Takazudo/zudo-led-lamp/doc/src/content/docs/architecture/index.mdx

---
title: Architecture
sidebar_position: 1
---

The locked prototype architecture — board split, net tables, final BOM, and the
decisions behind each. This is what the KiCad phase starts from.

<CategoryNav category="architecture" />
