Takazudo/zudo-led-lamp/doc/src/content/docs/power/index.mdx

---
title: Power
sidebar_position: 1
---

Board P — the USB-PD front end that negotiates a 15 V/3 A contract and hands a
switched rail downstream. Audited from the zudo-pd project, with every rating
re-checked against primary datasheets.

<CategoryNav category="power" />
