Takazudo/zudo-led-lamp/doc/src/content/docs/research/index.mdx

---
title: Research
sidebar_position: 1
---

Candidate research feeding the architecture decision — LED and driver options,
thermal budget, interconnect, and the control side (logic rail, MCU, knob,
modulation). Options here are deliberately left open; the picks live in
Architecture.

<CategoryNav category="research" />
