Takazudo/zudo-led-lamp/doc/src/content/docs/components/integration/index.mdx

---
# GENERATED by doc/component-docs — do not edit; run `pnpm generate:components`
title: "Integration"
description: "Cross-component rules — rule-rail-envelope, rule-usb-pd-nvm-load-switch, rule-al8860-led-stage, rule-ap63203-logic-stage, rule-ntc-adc-firmware, rule-evidence-chain, rule-c5446803-power-cut, rule-c470643-brightness-adc — with the records and facts each spans, its conditioned calculations, and what it refuses to conclude."
sidebar_position: 4
---

A component record answers questions about one part. These rules answer the ones that span several — whether a divider built from two resistors keeps a third part inside its own limit, whether a clamp event stays under everything downstream of it. Each rule is projected whole from stored evidence: its conditions, the exact facts it rests on, any conditioned arithmetic, and the exact wording of what it refuses to conclude.

## How to read these rules

- **The refusal is the rule.** — Every rule states, in its own words, what may NOT be concluded from the evidence above it. That sentence is the rule's real output; the verdict is shorthand for it.
- **A verdict belongs to the rule, not to a part.** — A rule's verdict says how far the cross-component question has been settled. It is never a judgement about any of the parts the rule names, and the verdicts are never combined into one.
- **Calculations are conditioned, and the conditions are the point.** — Each calculation publishes its expression, its inputs and the exact results that were recorded, together with the conditions under which the answer means anything. A result read without them is arithmetic mistaken for a measurement.
- **Numbers here were carried, not computed.** — The expressions are published so a reader can redo the arithmetic. This page does not evaluate them — the results shown are the ones the evidence recorded.
- **An evidence chain does not flow downhill.** — A stage being settled says nothing about any stage after it. A document confirming a limit is not a measurement of the assembled board.

## Rules at a glance

<EvidenceAnchor id="integration-index" />

<EvidenceTable label="rules-index">
  | Rule                                                          | Domain                             | Records | Facts | Verdict     |
  | ------------------------------------------------------------- | ---------------------------------- | ------- | ----- | ----------- |
  | [`rule-rail-envelope`](#rule-rail-envelope)                   | rail-envelope                      | 13      | 22    | UNSOURCED   |
  | [`rule-usb-pd-nvm-load-switch`](#rule-usb-pd-nvm-load-switch) | usb-pd-nvm-load-switch             | 9       | 18    | UNSOURCED   |
  | [`rule-al8860-led-stage`](#rule-al8860-led-stage)             | al8860-led-stage                   | 7       | 25    | NEEDS BENCH |
  | [`rule-ap63203-logic-stage`](#rule-ap63203-logic-stage)       | ap63203-logic-stage                | 4       | 16    | UNSOURCED   |
  | [`rule-ntc-adc-firmware`](#rule-ntc-adc-firmware)             | ntc-adc-firmware                   | 3       | 9     | UNSOURCED   |
  | [`rule-evidence-chain`](#rule-evidence-chain)                 | source-to-bench-chain              | 5       | 8     | NEEDS BENCH |
  | [`rule-c5446803-power-cut`](#rule-c5446803-power-cut)         | board-mounted lamp power switching | 4       | 5     | NEEDS BENCH |
  | [`rule-c470643-brightness-adc`](#rule-c470643-brightness-adc) | potentiometer-brightness-adc       | 5       | 12    | NEEDS BENCH |
</EvidenceTable>

## rule-rail-envelope

<EvidenceAnchor id="rule-rail-envelope" />

**What this rule asks:** Whether every part on the input rail stays inside its own recorded limits across a legal power contract, a mis-contract, and a transient clamp event.

**Domain:** rail-envelope

**Verdict:** UNSOURCED

**This rule refuses to conclude:** Do not declare the complete rail safe while STUSB primary trust, project mapping, actual clamp/source-impedance waveform, and harness/as-built evidence remain open.

**Conditions:** Separate legal 5/15 V operation, 20 V mis-contract, and transient clamp behavior; connector-pair current, direct-board mechanics, and upstream source impedance remain independent conditions.

**Records this rule spans:**

- [`rec-type-c-31-m-17`](/docs/components/records/type-c-31-m-17/) — TYPE-C-31-M-17
- [`rec-stusb4500qtr`](/docs/components/records/stusb4500qtr/) — STUSB4500QTR
- [`rec-high-diode-smaj20a`](/docs/components/records/high-diode-smaj20a/) — SMAJ20A
- [`rec-umw-ao3401a`](/docs/components/records/umw-ao3401a/) — AO3401A
- [`rec-bsmd1206-075-30v`](/docs/components/records/bsmd1206-075-30v/) — BSMD1206-075-30V
- [`rec-al8860mp-13`](/docs/components/records/al8860mp-13/) — AL8860MP-13
- [`rec-ap63203wu-7`](/docs/components/records/ap63203wu-7/) — AP63203WU-7
- [`rec-c492405`](/docs/components/records/c492405/) — PZ254V-11-06P
- [`rec-c2832269`](/docs/components/records/c2832269/) — PM254V-11-06-H85
- [`rec-c13585`](/docs/components/records/c13585/) — CL31A106KBHNNNE
- [`rec-c14663`](/docs/components/records/c14663/) — CC0603KRX7R9BB104
- [`rec-c15849`](/docs/components/records/c15849/) — CL10A105KB8NNNC
- [`rec-cl21a226maqnnne`](/docs/components/records/cl21a226maqnnne/) — CL21A226MAQNNNE

**Facts this rule rests on:** each is published in full on the record page that owns it, at the anchor linked here.

- [`fact-type-c-31-m-17-ratings`](/docs/components/records/type-c-31-m-17/#fact-type-c-31-m-17-ratings) on TYPE-C-31-M-17
- [`fact-stusb-supplies`](/docs/components/records/stusb4500qtr/#fact-stusb-supplies) on STUSB4500QTR
- [`fact-stusb-vdd-absolute-max`](/docs/components/records/stusb4500qtr/#fact-stusb-vdd-absolute-max) on STUSB4500QTR
- [`fact-stusb-cc-absolute-max`](/docs/components/records/stusb4500qtr/#fact-stusb-cc-absolute-max) on STUSB4500QTR
- [`fact-stusb-vbus-pin-absolute-max`](/docs/components/records/stusb4500qtr/#fact-stusb-vbus-pin-absolute-max) on STUSB4500QTR
- [`fact-high-diode-smaj20a-clamp`](/docs/components/records/high-diode-smaj20a/#fact-high-diode-smaj20a-clamp) on SMAJ20A
- [`fact-umw-ao3401a-vds`](/docs/components/records/umw-ao3401a/#fact-umw-ao3401a-vds) on AO3401A
- [`fact-umw-ao3401a-vgs`](/docs/components/records/umw-ao3401a/#fact-umw-ao3401a-vgs) on AO3401A
- [`fact-bhfuse-voltage-max`](/docs/components/records/bsmd1206-075-30v/#fact-bhfuse-voltage-max) on BSMD1206-075-30V
- [`fact-al8860-vin-recommended-max`](/docs/components/records/al8860mp-13/#fact-al8860-vin-recommended-max) on AL8860MP-13
- [`fact-al8860-vin-absolute-max`](/docs/components/records/al8860mp-13/#fact-al8860-vin-absolute-max) on AL8860MP-13
- [`fact-ap63203-vin-recommended-max`](/docs/components/records/ap63203wu-7/#fact-ap63203-vin-recommended-max) on AP63203WU-7
- [`fact-ap63203-vin-absolute-dc`](/docs/components/records/ap63203wu-7/#fact-ap63203-vin-absolute-dc) on AP63203WU-7
- [`fact-ap63203-vin-transient`](/docs/components/records/ap63203wu-7/#fact-ap63203-vin-transient) on AP63203WU-7
- [`fact-c492405-current`](/docs/components/records/c492405/#fact-c492405-current) on PZ254V-11-06P
- [`fact-c492405-voltage`](/docs/components/records/c492405/#fact-c492405-voltage) on PZ254V-11-06P
- [`fact-c2832269-current`](/docs/components/records/c2832269/#fact-c2832269-current) on PM254V-11-06-H85
- [`fact-c2832269-voltage`](/docs/components/records/c2832269/#fact-c2832269-voltage) on PM254V-11-06-H85
- [`fact-c13585-voltage`](/docs/components/records/c13585/#fact-c13585-voltage) on CL31A106KBHNNNE
- [`fact-c14663-voltage`](/docs/components/records/c14663/#fact-c14663-voltage) on CC0603KRX7R9BB104
- [`fact-c15849-voltage`](/docs/components/records/c15849/#fact-c15849-voltage) on CL10A105KB8NNNC
- [`fact-cl21-voltage`](/docs/components/records/cl21a226maqnnne/#fact-cl21-voltage) on CL21A226MAQNNNE

### Conditioned calculations

Arithmetic across the facts above. The expression and every input are published so the result can be recomputed rather than trusted, and each carries the conditions under which it means anything at all.

#### calc-stusb-vdd-clamp-overage

<EvidenceAnchor id="calc-stusb-vdd-clamp-overage" />

**Expression:** `fact_high_diode_smaj20a_clamp - fact_stusb_vdd_absolute_max`

**Result:** `overage_v`

**Conditions:** conditioned subtraction of the mirrored 28 V VDD absolute maximum from the High Diode 32.4 V table clamp point; UNSOURCED and not proof of the real VDD transient waveform

**Inputs:**

- [`fact-stusb-vdd-absolute-max`](/docs/components/records/stusb4500qtr/#fact-stusb-vdd-absolute-max) on STUSB4500QTR
- [`fact-high-diode-smaj20a-clamp`](/docs/components/records/high-diode-smaj20a/#fact-high-diode-smaj20a-clamp) on SMAJ20A

| overage\_v |
| ---------- |
| 4.4        |

#### calc-q1-vds-clamp-overage

<EvidenceAnchor id="calc-q1-vds-clamp-overage" />

**Expression:** `fact_high_diode_smaj20a_clamp + fact_umw_ao3401a_vds`

**Result:** `overage_v`

**Conditions:** conditioned magnitude overage above the -30 V Q1 VDS absolute maximum at the 32.4 V clamp table point; actual polarity, waveform, parasitics and as-built state remain open

**Inputs:**

- [`fact-umw-ao3401a-vds`](/docs/components/records/umw-ao3401a/#fact-umw-ao3401a-vds) on AO3401A
- [`fact-high-diode-smaj20a-clamp`](/docs/components/records/high-diode-smaj20a/#fact-high-diode-smaj20a-clamp) on SMAJ20A

| overage\_v |
| ---------- |
| 2.4        |

## rule-usb-pd-nvm-load-switch

<EvidenceAnchor id="rule-usb-pd-nvm-load-switch" />

**What this rule asks:** How the power-delivery controller's stored configuration and its enable output drive the load switch, through every state from detached to fault.

**Domain:** usb-pd-nvm-load-switch

**Verdict:** UNSOURCED

**This rule refuses to conclude:** Do not infer PDOs, VBEN default policy, fitted Rd state, programmed/read-back NVM bytes, or a deterministic 32.4 V VGS violation/safe result without the actual VBEN/gate/source waveform, duration, device/parasitic model, as-built state, and bench evidence.

**Conditions:** Evaluate detached, dead-battery, reset, NVM-loaded, attached, hard-reset, fault, and disconnect states. With VBEN held low and ideal nominal resistors, VGS=-VBUS\*100k/(100k+150k): -6.0 V at 15 V, -8.0 V at 20 V, and -12.96 V at 32.4 V. C35 is gate-to-source, so the nominal small-signal gate time constant is (100k parallel 150k)\*100 nF about 6 ms; device/parasitic behavior and the actual transient waveform remain separate.

**Records this rule spans:**

- [`rec-stusb4500qtr`](/docs/components/records/stusb4500qtr/) — STUSB4500QTR
- [`rec-umw-ao3401a`](/docs/components/records/umw-ao3401a/) — AO3401A
- [`rec-c25803`](/docs/components/records/c25803/) — 0603WAF1003T5E
- [`rec-c22807`](/docs/components/records/c22807/) — 0603WAF1503T5E
- [`rec-c14663`](/docs/components/records/c14663/) — CC0603KRX7R9BB104
- [`rec-c21189`](/docs/components/records/c21189/) — 0603WAF0000T5E
- [`rec-rd-0603waf5101t5e`](/docs/components/records/rd-0603waf5101t5e/) — 0603WAF5101T5E
- [`rec-al8860mp-13`](/docs/components/records/al8860mp-13/) — AL8860MP-13
- [`rec-ap63203wu-7`](/docs/components/records/ap63203wu-7/) — AP63203WU-7

**Facts this rule rests on:** each is published in full on the record page that owns it, at the anchor linked here.

- [`fact-stusb-pin-states`](/docs/components/records/stusb4500qtr/#fact-stusb-pin-states) on STUSB4500QTR
- [`fact-stusb-vben`](/docs/components/records/stusb4500qtr/#fact-stusb-vben) on STUSB4500QTR
- [`fact-stusb-nvm-load`](/docs/components/records/stusb4500qtr/#fact-stusb-nvm-load) on STUSB4500QTR
- [`fact-stusb-volatile-pdo`](/docs/components/records/stusb4500qtr/#fact-stusb-volatile-pdo) on STUSB4500QTR
- [`fact-stusb-artifact`](/docs/components/records/stusb4500qtr/#fact-stusb-artifact) on STUSB4500QTR
- [`fact-umw-ao3401a-vgs`](/docs/components/records/umw-ao3401a/#fact-umw-ao3401a-vgs) on AO3401A
- [`fact-umw-ao3401a-project-nets`](/docs/components/records/umw-ao3401a/#fact-umw-ao3401a-project-nets) on AO3401A
- [`fact-c25803-resistance`](/docs/components/records/c25803/#fact-c25803-resistance) on 0603WAF1003T5E
- [`fact-c22807-resistance`](/docs/components/records/c22807/#fact-c22807-resistance) on 0603WAF1503T5E
- [`fact-c22807-r12-topology`](/docs/components/records/c22807/#fact-c22807-r12-topology) on 0603WAF1503T5E
- [`fact-c14663-capacitance`](/docs/components/records/c14663/#fact-c14663-capacitance) on CC0603KRX7R9BB104
- [`fact-c14663-c35-topology`](/docs/components/records/c14663/#fact-c14663-c35-topology) on CC0603KRX7R9BB104
- [`fact-c21189-ccdb-topology`](/docs/components/records/c21189/#fact-c21189-ccdb-topology) on 0603WAF0000T5E
- [`fact-rd-fit-state`](/docs/components/records/rd-0603waf5101t5e/#fact-rd-fit-state) on 0603WAF5101T5E
- [`fact-al8860-project-nets`](/docs/components/records/al8860mp-13/#fact-al8860-project-nets) on AL8860MP-13
- [`fact-al8860-ctrl`](/docs/components/records/al8860mp-13/#fact-al8860-ctrl) on AL8860MP-13
- [`fact-ap63203-project-nets`](/docs/components/records/ap63203wu-7/#fact-ap63203-project-nets) on AP63203WU-7
- [`fact-ap63203-en-open`](/docs/components/records/ap63203wu-7/#fact-ap63203-en-open) on AP63203WU-7

### Conditioned calculations

Arithmetic across the facts above. The expression and every input are published so the result can be recomputed rather than trusted, and each carries the conditions under which it means anything at all.

#### calc-q1-steady-vgs

<EvidenceAnchor id="calc-q1-steady-vgs" />

**Expression:** `-vbus_v * fact_c25803_resistance / (fact_c25803_resistance + fact_c22807_resistance)`

**Result:** `vgs_v`

**Conditions:** ideal steady VBEN-low divider only; absolute maximum is not an operating target

**Inputs:**

- [`fact-stusb-vben`](/docs/components/records/stusb4500qtr/#fact-stusb-vben) on STUSB4500QTR
- [`fact-c25803-resistance`](/docs/components/records/c25803/#fact-c25803-resistance) on 0603WAF1003T5E
- [`fact-c22807-resistance`](/docs/components/records/c22807/#fact-c22807-resistance) on 0603WAF1503T5E
- [`fact-c22807-r12-topology`](/docs/components/records/c22807/#fact-c22807-r12-topology) on 0603WAF1503T5E

| vbus\_v | vgs\_v |
| --- | --- |
| 15 | -6 |
| 20 | -8 |
| 32.4 | -12.96 |

#### calc-q1-steady-vgs-margin

<EvidenceAnchor id="calc-q1-steady-vgs-margin" />

**Expression:** `fact_umw_ao3401a_vgs - vbus_v * fact_c25803_resistance / (fact_c25803_resistance + fact_c22807_resistance)`

**Result:** `margin_v`

**Conditions:** ideal steady VBEN-low magnitude margin to the 12 V absolute maximum; the negative 32.4 V ideal-steady result is not a deterministic claim about the real transient waveform

**Inputs:**

- [`fact-umw-ao3401a-vgs`](/docs/components/records/umw-ao3401a/#fact-umw-ao3401a-vgs) on AO3401A
- [`fact-c25803-resistance`](/docs/components/records/c25803/#fact-c25803-resistance) on 0603WAF1003T5E
- [`fact-c22807-resistance`](/docs/components/records/c22807/#fact-c22807-resistance) on 0603WAF1503T5E
- [`fact-c22807-r12-topology`](/docs/components/records/c22807/#fact-c22807-r12-topology) on 0603WAF1503T5E

| vbus\_v | margin\_v |
| --- | --- |
| 15 | 6 |
| 20 | 4 |
| 32.4 | -0.96 |

#### calc-q1-gate-tau

<EvidenceAnchor id="calc-q1-gate-tau" />

**Expression:** `(fact_c25803_resistance * fact_c22807_resistance / (fact_c25803_resistance + fact_c22807_resistance)) * fact_c14663_capacitance * 1e-6`

**Result:** `result_s`

**Conditions:** fact-c14663 capacitance is expressed in uF; nominal small-signal RC only; excludes MOSFET capacitance, STUSB output impedance, PCB parasitics and nonlinear switching

**Inputs:**

- [`fact-c25803-resistance`](/docs/components/records/c25803/#fact-c25803-resistance) on 0603WAF1003T5E
- [`fact-c22807-resistance`](/docs/components/records/c22807/#fact-c22807-resistance) on 0603WAF1503T5E
- [`fact-c14663-capacitance`](/docs/components/records/c14663/#fact-c14663-capacitance) on CC0603KRX7R9BB104
- [`fact-c14663-c35-topology`](/docs/components/records/c14663/#fact-c14663-c35-topology) on CC0603KRX7R9BB104

| result\_s |
| --------- |
| 0.006     |

## rule-al8860-led-stage

<EvidenceAnchor id="rule-al8860-led-stage" />

**What this rule asks:** How the LED driver, its sense resistor, inductor, catch diode and per-branch ballast behave together across the LED forward-voltage, tolerance and temperature envelope.

**Domain:** al8860-led-stage

**Verdict:** NEEDS BENCH

**This rule refuses to conclude:** Do not promote mirror-only FXL or R+O SS26 limits, assumed branch sharing, or nominal arithmetic to a guaranteed selected-stage PASS.

**Conditions:** Use the full LED Vf/current/temperature envelope, resistor tolerance/TCR, magnetic current definition, diode polarity/waveform, ballast sharing, CTRL/PWM state, PCB thermal path, and fault behavior.; per-branch sharing is bounded by a locked 0.30 V acceptance limit on the assembled 3-LED string forward-voltage spread

**Records this rule spans:**

- [`rec-al8860mp-13`](/docs/components/records/al8860mp-13/) — AL8860MP-13
- [`rec-rlp25feer200`](/docs/components/records/rlp25feer200/) — RLP25FEER200
- [`rec-fxl0630-330-m`](/docs/components/records/fxl0630-330-m/) — FXL0630-330-M
- [`rec-ro-ss26`](/docs/components/records/ro-ss26/) — SS26
- [`rec-c210315`](/docs/components/records/c210315/) — HL-AM-2835H421W-S1-08-HR3
- [`rec-c2934070`](/docs/components/records/c2934070/) — FRC2512F33R0TS
- [`rec-c4216`](/docs/components/records/c4216/) — 0603WAF3302T5E

**Facts this rule rests on:** each is published in full on the record page that owns it, at the anchor linked here.

- [`fact-al8860-sense-min`](/docs/components/records/al8860mp-13/#fact-al8860-sense-min) on AL8860MP-13
- [`fact-al8860-sense-max`](/docs/components/records/al8860mp-13/#fact-al8860-sense-max) on AL8860MP-13
- [`fact-al8860-current-min`](/docs/components/records/al8860mp-13/#fact-al8860-current-min) on AL8860MP-13
- [`fact-al8860-current-max`](/docs/components/records/al8860mp-13/#fact-al8860-current-max) on AL8860MP-13
- [`fact-al8860-peak-current`](/docs/components/records/al8860mp-13/#fact-al8860-peak-current) on AL8860MP-13
- [`fact-al8860-ctrl`](/docs/components/records/al8860mp-13/#fact-al8860-ctrl) on AL8860MP-13
- [`fact-al8860-faults`](/docs/components/records/al8860mp-13/#fact-al8860-faults) on AL8860MP-13
- [`fact-rlp25-resistance-min`](/docs/components/records/rlp25feer200/#fact-rlp25-resistance-min) on RLP25FEER200
- [`fact-rlp25-resistance-max`](/docs/components/records/rlp25feer200/#fact-rlp25-resistance-max) on RLP25FEER200
- [`fact-rlp25-power-margin`](/docs/components/records/rlp25feer200/#fact-rlp25-power-margin) on RLP25FEER200
- [`fact-fxl-isat-margin`](/docs/components/records/fxl0630-330-m/#fact-fxl-isat-margin) on FXL0630-330-M
- [`fact-ss26-polarity`](/docs/components/records/ro-ss26/#fact-ss26-polarity) on SS26
- [`fact-c210315-vf-min`](/docs/components/records/c210315/#fact-c210315-vf-min) on HL-AM-2835H421W-S1-08-HR3
- [`fact-c210315-vf-max`](/docs/components/records/c210315/#fact-c210315-vf-max) on HL-AM-2835H421W-S1-08-HR3
- [`fact-c210315-forward-current-max`](/docs/components/records/c210315/#fact-c210315-forward-current-max) on HL-AM-2835H421W-S1-08-HR3
- [`fact-c210315-power-max`](/docs/components/records/c210315/#fact-c210315-power-max) on HL-AM-2835H421W-S1-08-HR3
- [`fact-c210315-reverse-voltage-max`](/docs/components/records/c210315/#fact-c210315-reverse-voltage-max) on HL-AM-2835H421W-S1-08-HR3
- [`fact-c210315-junction-temperature-max`](/docs/components/records/c210315/#fact-c210315-junction-temperature-max) on HL-AM-2835H421W-S1-08-HR3
- [`fact-c210315-solder-temperature-max`](/docs/components/records/c210315/#fact-c210315-solder-temperature-max) on HL-AM-2835H421W-S1-08-HR3
- [`fact-c2934070-resistance`](/docs/components/records/c2934070/#fact-c2934070-resistance) on FRC2512F33R0TS
- [`fact-c2934070-power`](/docs/components/records/c2934070/#fact-c2934070-power) on FRC2512F33R0TS
- [`fact-c2934070-rcwv`](/docs/components/records/c2934070/#fact-c2934070-rcwv) on FRC2512F33R0TS
- [`fact-c2934070-topology`](/docs/components/records/c2934070/#fact-c2934070-topology) on FRC2512F33R0TS
- [`fact-c2934070-tolerance`](/docs/components/records/c2934070/#fact-c2934070-tolerance) on FRC2512F33R0TS
- [`fact-c4216-ctrl-topology`](/docs/components/records/c4216/#fact-c4216-ctrl-topology) on 0603WAF3302T5E

### Conditioned calculations

Arithmetic across the facts above. The expression and every input are published so the result can be recomputed rather than trusted, and each carries the conditions under which it means anything at all.

#### calc-led-hot-branch-peak

<EvidenceAnchor id="calc-led-hot-branch-peak" />

**Expression:** `(fact_al8860_peak_current + 7 * spread_v / (fact_c2934070_resistance * (1 + fact_c2934070_tolerance / 100))) / (1 + 7 * (1 - fact_c2934070_tolerance / 100) / (1 + fact_c2934070_tolerance / 100))`

**Result:** `current_a`

**Conditions:** hottest of eight parallel ballast branches at the AL8860 upper peak current, with the hot branch at minimum ballast tolerance and the other seven at maximum; spread\_v is the assembled 3-LED string forward-voltage spread in volts (0 = perfectly matched, 0.3 = the locked acceptance limit, 1.8 = the full retained 2.6-3.2 V window unmitigated); LEDs modelled as fixed forward drops, so this is not proof of the real installed sharing

**Inputs:**

- [`fact-al8860-peak-current`](/docs/components/records/al8860mp-13/#fact-al8860-peak-current) on AL8860MP-13
- [`fact-c2934070-resistance`](/docs/components/records/c2934070/#fact-c2934070-resistance) on FRC2512F33R0TS
- [`fact-c2934070-tolerance`](/docs/components/records/c2934070/#fact-c2934070-tolerance) on FRC2512F33R0TS

| spread\_v | current\_a |
| --- | --- |
| 0 | 0.08017708571864743 |
| 0.3 | 0.08819174108846653 |
| 1.8 | 0.128265017937562 |

#### calc-led-hot-branch-headroom

<EvidenceAnchor id="calc-led-hot-branch-headroom" />

**Expression:** `fact_c210315_forward_current_max - 1000 * (fact_al8860_peak_current + 7 * spread_v / (fact_c2934070_resistance * (1 + fact_c2934070_tolerance / 100))) / (1 + 7 * (1 - fact_c2934070_tolerance / 100) / (1 + fact_c2934070_tolerance / 100))`

**Result:** `headroom_ma`

**Conditions:** milliamp headroom from the hottest branch peak to the 90 mA LED absolute maximum; the spread\_v = 0 result shows the driver's own worst case already consumes 89 percent of the absolute maximum before any Vf mismatch, and spread\_v = 1.8 is negative; absolute maximum is not an operating target and no pulsed-current rating is retained

**Inputs:**

- [`fact-c210315-forward-current-max`](/docs/components/records/c210315/#fact-c210315-forward-current-max) on HL-AM-2835H421W-S1-08-HR3
- [`fact-al8860-peak-current`](/docs/components/records/al8860mp-13/#fact-al8860-peak-current) on AL8860MP-13
- [`fact-c2934070-resistance`](/docs/components/records/c2934070/#fact-c2934070-resistance) on FRC2512F33R0TS
- [`fact-c2934070-tolerance`](/docs/components/records/c2934070/#fact-c2934070-tolerance) on FRC2512F33R0TS

| spread\_v | headroom\_ma |
| --- | --- |
| 0 | 9.822914281352567  |
| 0.3 | 1.8082589115334713 |
| 1.8 | -38.26501793756202 |

## rule-ap63203-logic-stage

<EvidenceAnchor id="rule-ap63203-logic-stage" />

**What this rule asks:** How the logic-rail converter, its inductor and its output capacitor behave together under the real load the microcontroller presents.

**Domain:** ap63203-logic-stage

**Verdict:** UNSOURCED

**This rule refuses to conclude:** Do not infer minimum off-time, MCU load, guaranteed MLCC capacitance, or full-load FNR thermal margin from nominal values.

**Conditions:** Check V15 transients, EN-open startup, switching timing, actual V3P3 load steps, inductor heating/saturation, effective output capacitance, layout, and MCU operating state.

**Records this rule spans:**

- [`rec-ap63203wu-7`](/docs/components/records/ap63203wu-7/) — AP63203WU-7
- [`rec-fnr4030s4r7mt`](/docs/components/records/fnr4030s4r7mt/) — FNR4030S4R7MT
- [`rec-cl21a226maqnnne`](/docs/components/records/cl21a226maqnnne/) — CL21A226MAQNNNE
- [`rec-c529334`](/docs/components/records/c529334/) — STM32G031F8P6

**Facts this rule rests on:** each is published in full on the record page that owns it, at the anchor linked here.

- [`fact-ap63203-vin-recommended-max`](/docs/components/records/ap63203wu-7/#fact-ap63203-vin-recommended-max) on AP63203WU-7
- [`fact-ap63203-vin-absolute-dc`](/docs/components/records/ap63203wu-7/#fact-ap63203-vin-absolute-dc) on AP63203WU-7
- [`fact-ap63203-vin-transient`](/docs/components/records/ap63203wu-7/#fact-ap63203-vin-transient) on AP63203WU-7
- [`fact-ap63203-en-open`](/docs/components/records/ap63203wu-7/#fact-ap63203-en-open) on AP63203WU-7
- [`fact-ap63203-frequency`](/docs/components/records/ap63203wu-7/#fact-ap63203-frequency) on AP63203WU-7
- [`fact-ap63203-min-on-time`](/docs/components/records/ap63203wu-7/#fact-ap63203-min-on-time) on AP63203WU-7
- [`fact-ap63203-min-off-time`](/docs/components/records/ap63203wu-7/#fact-ap63203-min-off-time) on AP63203WU-7
- [`fact-ap63203-required-inductor-current`](/docs/components/records/ap63203wu-7/#fact-ap63203-required-inductor-current) on AP63203WU-7
- [`fact-ap63203-cap-min`](/docs/components/records/ap63203wu-7/#fact-ap63203-cap-min) on AP63203WU-7
- [`fact-ap63203-cap-max`](/docs/components/records/ap63203wu-7/#fact-ap63203-cap-max) on AP63203WU-7
- [`fact-ap63203-thermal`](/docs/components/records/ap63203wu-7/#fact-ap63203-thermal) on AP63203WU-7
- [`fact-fnr-isat-margin`](/docs/components/records/fnr4030s4r7mt/#fact-fnr-isat-margin) on FNR4030S4R7MT
- [`fact-fnr-irated-margin`](/docs/components/records/fnr4030s4r7mt/#fact-fnr-irated-margin) on FNR4030S4R7MT
- [`fact-cl21-dc-bias`](/docs/components/records/cl21a226maqnnne/#fact-cl21-dc-bias) on CL21A226MAQNNNE
- [`fact-cl21-effective-capacitance-status`](/docs/components/records/cl21a226maqnnne/#fact-cl21-effective-capacitance-status) on CL21A226MAQNNNE
- [`fact-c529334-topology`](/docs/components/records/c529334/#fact-c529334-topology) on STM32G031F8P6

**Conditioned calculations:** none are recorded for this rule.

## rule-ntc-adc-firmware

<EvidenceAnchor id="rule-ntc-adc-firmware" />

**What this rule asks:** How the thermistor, its divider, the analog-to-digital input and the firmware that reads them combine into a temperature the design can act on.

**Domain:** ntc-adc-firmware

**Verdict:** UNSOURCED

**This rule refuses to conclude:** Do not invent firmware thresholds or use beta-only conversion as a guaranteed full R-T curve.

**Conditions:** Evaluate NTC tolerance and R-T data, divider loading, ADC sample time/source impedance, calibration, placement/thermal lag, and actual firmware thresholds/hysteresis.; the divider top is 100 kOhm C25803 and the ADC channel requires the 160.5-cycle sample time, with a stated sensing validity floor of -20 C at RT1

**Records this rule spans:**

- [`rec-c13564`](/docs/components/records/c13564/) — NCP18XH103F03RB
- [`rec-c529334`](/docs/components/records/c529334/) — STM32G031F8P6
- [`rec-c25803`](/docs/components/records/c25803/) — 0603WAF1003T5E

**Facts this rule rests on:** each is published in full on the record page that owns it, at the anchor linked here.

- [`fact-c13564-resistance`](/docs/components/records/c13564/#fact-c13564-resistance) on NCP18XH103F03RB
- [`fact-c13564-beta`](/docs/components/records/c13564/#fact-c13564-beta) on NCP18XH103F03RB
- [`fact-c13564-max-current`](/docs/components/records/c13564/#fact-c13564-max-current) on NCP18XH103F03RB
- [`fact-c13564-topology`](/docs/components/records/c13564/#fact-c13564-topology) on NCP18XH103F03RB
- [`fact-c13564-curve-caveat`](/docs/components/records/c13564/#fact-c13564-curve-caveat) on NCP18XH103F03RB
- [`fact-c529334-adc`](/docs/components/records/c529334/#fact-c529334-adc) on STM32G031F8P6
- [`fact-c529334-topology`](/docs/components/records/c529334/#fact-c529334-topology) on STM32G031F8P6
- [`fact-c25803-resistance`](/docs/components/records/c25803/#fact-c25803-resistance) on 0603WAF1003T5E
- [`fact-c25803-tolerance`](/docs/components/records/c25803/#fact-c25803-tolerance) on 0603WAF1003T5E

### Conditioned calculations

Arithmetic across the facts above. The expression and every input are published so the result can be recomputed rather than trusted, and each carries the conditions under which it means anything at all.

#### calc-ntc-divider-current-margin

<EvidenceAnchor id="calc-ntc-divider-current-margin" />

**Expression:** `fact_c13564_max_current - 1000 * rail_v / (fact_c25803_resistance * (1 - fact_c25803_tolerance / 100))`

**Result:** `margin_ma`

**Conditions:** bounding divider current at R26 minimum with the NTC treated as a short, so the result holds at every temperature and under a shorted-thermistor fault; rail\_v 3.33 is fact-ap63203-vout-max and 3.3 is nominal; positive margin\_ma means the installed current stays under Murata's 0.1 mA operating maximum; not a measurement of the real installed current

**Inputs:**

- [`fact-c13564-max-current`](/docs/components/records/c13564/#fact-c13564-max-current) on NCP18XH103F03RB
- [`fact-c25803-resistance`](/docs/components/records/c25803/#fact-c25803-resistance) on 0603WAF1003T5E
- [`fact-c25803-tolerance`](/docs/components/records/c25803/#fact-c25803-tolerance) on 0603WAF1003T5E

| rail\_v | margin\_ma |
| --- | --- |
| 3.33 | 0.06636363636363637 |
| 3.3 | 0.06666666666666668 |

#### calc-ntc-adc-source-impedance

<EvidenceAnchor id="calc-ntc-adc-source-impedance" />

**Expression:** `fact_c25803_resistance * (1 + fact_c25803_tolerance / 100) * r_ntc_ohm / (fact_c25803_resistance * (1 + fact_c25803_tolerance / 100) + r_ntc_ohm)`

**Result:** `r_source_ohm`

**Conditions:** ADC source resistance at R26 maximum; the r\_ntc\_ohm inputs are beta-derived cold-end maxima (-20 C and 25 C) from fact-c13564-resistance and fact-c13564-beta at R25 max and B max, not a guaranteed R-T table per fact-c13564-curve-caveat; compare against the 50 kOhm allowance at 160.5 cycles in fact-c529334-adc

**Inputs:**

- [`fact-c25803-resistance`](/docs/components/records/c25803/#fact-c25803-resistance) on 0603WAF1003T5E
- [`fact-c25803-tolerance`](/docs/components/records/c25803/#fact-c25803-tolerance) on 0603WAF1003T5E

| r\_ntc\_ohm | r\_source\_ohm |
| --- | --- |
| 77314.35 | 43792.0411340983  |
| 10100 | 9181.818181818182 |

## rule-evidence-chain

<EvidenceAnchor id="rule-evidence-chain" />

**What this rule asks:** How far each claim has travelled from a manufacturer document towards a measurement on real hardware, stage by stage.

**Domain:** source-to-bench-chain

**Verdict:** NEEDS BENCH

**This rule refuses to conclude:** A completed upstream stage never implies a later as-built, programmed, or measured stage.

**Conditions:** Trace each claim through official source, conditioned requirement, generated netlist, symbol/footprint pin map, PCB/BOM/CPL identity, as-built inspection, programmed state, and bench evidence.

**Records this rule spans:**

- [`rec-stusb4500qtr`](/docs/components/records/stusb4500qtr/) — STUSB4500QTR
- [`rec-umw-ao3401a`](/docs/components/records/umw-ao3401a/) — AO3401A
- [`rec-al8860mp-13`](/docs/components/records/al8860mp-13/) — AL8860MP-13
- [`rec-ap63203wu-7`](/docs/components/records/ap63203wu-7/) — AP63203WU-7
- [`rec-c529334`](/docs/components/records/c529334/) — STM32G031F8P6

**Facts this rule rests on:** each is published in full on the record page that owns it, at the anchor linked here.

- [`fact-stusb-vben`](/docs/components/records/stusb4500qtr/#fact-stusb-vben) on STUSB4500QTR
- [`fact-stusb-artifact`](/docs/components/records/stusb4500qtr/#fact-stusb-artifact) on STUSB4500QTR
- [`fact-umw-ao3401a-vgs`](/docs/components/records/umw-ao3401a/#fact-umw-ao3401a-vgs) on AO3401A
- [`fact-umw-ao3401a-pinout`](/docs/components/records/umw-ao3401a/#fact-umw-ao3401a-pinout) on AO3401A
- [`fact-umw-ao3401a-project-nets`](/docs/components/records/umw-ao3401a/#fact-umw-ao3401a-project-nets) on AO3401A
- [`fact-al8860-project-nets`](/docs/components/records/al8860mp-13/#fact-al8860-project-nets) on AL8860MP-13
- [`fact-ap63203-project-nets`](/docs/components/records/ap63203wu-7/#fact-ap63203-project-nets) on AP63203WU-7
- [`fact-c529334-topology`](/docs/components/records/c529334/#fact-c529334-topology) on STM32G031F8P6

**Conditioned calculations:** none are recorded for this rule.

### Source-to-bench evidence chain

The stages a claim passes through, in order. A settled stage says nothing about any stage after it: a manufacturer document confirming a limit is not an inspection of the assembled board, and neither is a measurement. A stage with no facts against it is not one nobody got round to filling in: nothing has been established there yet, so the rule's conditions and its refusal above are the whole of what is known about it.

<EvidenceTable label="evidence-chain">
  | Stage                   | Status | Facts at this stage                                                                                                                                                                                                                                                                                                                           |
  | ----------------------- | ------ | --------------------------------------------------------------------------------------------------------------------------------------------------------------------------------------------------------------------------------------------------------------------------------------------------------------------------------------------- |
  | official-source         | MIXED  | [`fact-stusb-vben`](/docs/components/records/stusb4500qtr/#fact-stusb-vben) on STUSB4500QTR, [`fact-umw-ao3401a-vgs`](/docs/components/records/umw-ao3401a/#fact-umw-ao3401a-vgs) on AO3401A                                                                                                                                                  |
  | conditioned-requirement | MIXED  | [`fact-stusb-artifact`](/docs/components/records/stusb4500qtr/#fact-stusb-artifact) on STUSB4500QTR, [`fact-umw-ao3401a-vgs`](/docs/components/records/umw-ao3401a/#fact-umw-ao3401a-vgs) on AO3401A                                                                                                                                          |
  | generated-netlist       | MIXED  | [`fact-umw-ao3401a-project-nets`](/docs/components/records/umw-ao3401a/#fact-umw-ao3401a-project-nets) on AO3401A, [`fact-al8860-project-nets`](/docs/components/records/al8860mp-13/#fact-al8860-project-nets) on AL8860MP-13, [`fact-ap63203-project-nets`](/docs/components/records/ap63203wu-7/#fact-ap63203-project-nets) on AP63203WU-7 |
  | symbol-footprint        | MIXED  | [`fact-umw-ao3401a-pinout`](/docs/components/records/umw-ao3401a/#fact-umw-ao3401a-pinout) on AO3401A, [`fact-c529334-topology`](/docs/components/records/c529334/#fact-c529334-topology) on STM32G031F8P6                                                                                                                                    |
  | pcb-orientation         | OPEN   | no fact is recorded at this stage                                                                                                                                                                                                                                                                                                             |
  | bom-cpl                 | OPEN   | no fact is recorded at this stage                                                                                                                                                                                                                                                                                                             |
  | as-built                | OPEN   | no fact is recorded at this stage                                                                                                                                                                                                                                                                                                             |
  | programmed              | OPEN   | no fact is recorded at this stage                                                                                                                                                                                                                                                                                                             |
  | bench                   | OPEN   | no fact is recorded at this stage                                                                                                                                                                                                                                                                                                             |
</EvidenceTable>

## rule-c5446803-power-cut

<EvidenceAnchor id="rule-c5446803-power-cut" />

**Domain:** board-mounted lamp power switching

**Verdict:** NEEDS BENCH

**This rule refuses to conclude:** Do not certify physical OFF isolation, installed height, switch endurance or rail safety from a mirrored current rating and generated design alone.

**Conditions:** SW2 center common 2 receives V15\_FUSED and joins outer pin 1 to switched V15 in ON. In OFF it joins isolated outer pin 3, which has no PCB net but is fused-feed live. Both converters lose normal supply in OFF while Board P remains powered. G020 has a 2 mm actuator and 5.5 mm body-plus-actuator dimension; the corrected model retains shoulder stand-off for approximately 6 mm PCB reach, requiring physical confirmation. Verify inrush, bounce, restart, contact life, rail decay and service-interface back-power. Exact switch drawing remains manufacturer-mirror evidence.

**Records this rule spans:**

- [`rec-c5446803`](/docs/components/records/c5446803/) — SS-12D01-G020
- [`rec-bsmd1206-075-30v`](/docs/components/records/bsmd1206-075-30v/) — BSMD1206-075-30V
- [`rec-al8860mp-13`](/docs/components/records/al8860mp-13/) — AL8860MP-13
- [`rec-ap63203wu-7`](/docs/components/records/ap63203wu-7/) — AP63203WU-7

**Facts this rule rests on:** each is published in full on the record page that owns it, at the anchor linked here.

- [`fact-c5446803-rating`](/docs/components/records/c5446803/#fact-c5446803-rating) on SS-12D01-G020
- [`fact-c5446803-terminals`](/docs/components/records/c5446803/#fact-c5446803-terminals) on SS-12D01-G020
- [`fact-c5446803-project-nets`](/docs/components/records/c5446803/#fact-c5446803-project-nets) on SS-12D01-G020
- [`fact-bhfuse-project-nets`](/docs/components/records/bsmd1206-075-30v/#fact-bhfuse-project-nets) on BSMD1206-075-30V
- [`fact-ap63203-en-open`](/docs/components/records/ap63203wu-7/#fact-ap63203-en-open) on AP63203WU-7

**Conditioned calculations:** none are recorded for this rule.

## rule-c470643-brightness-adc

<EvidenceAnchor id="rule-c470643-brightness-adc" />

**Domain:** potentiometer-brightness-adc

**Verdict:** NEEDS BENCH

**This rule refuses to conclude:** Do not claim calibrated absolute brightness, safe startup, open-wiper fault detection or installed mechanical fit from schematic calculations and unflashed firmware examples.

**Conditions:** RV1 RK10J11E0034 is the single-unit 10 kOhm +/-30% stopped potentiometer: end 1=GND, end 3=V3P3, wiper 2 through R27 100 Ohm to U3.7 PA0 BRIGHT\_ADC; all four mechanical pads and U3.8 are no-connects. R22 100 kOhm and C22 100 nF connect BRIGHT\_ADC to GND. Worst divider source resistance is 3.25 kOhm plus 100 Ohm before bias loading; open-wiper nominal RC decay is 10 ms, not a certified fault detector. Use the documented 160.5-cycle ADC target, reference/errata review, endpoint and inversion calibration, averaging and startup ramp with thermal/PD gates. The 270-degree physical stops replace quadrature behavior. The catalog lists Insertion (t: 2 mm); this is not treated as a mandatory PCB thickness. Seating and contact life on the actual 1.6 mm PCB need prototype proof, and firmware is not flashed.

**Records this rule spans:**

- [`rec-c470643`](/docs/components/records/c470643/) — RK10J11E0034
- [`rec-c529334`](/docs/components/records/c529334/) — STM32G031F8P6
- [`rec-c22775`](/docs/components/records/c22775/) — 0603WAF1000T5E
- [`rec-c25803`](/docs/components/records/c25803/) — 0603WAF1003T5E
- [`rec-c14663`](/docs/components/records/c14663/) — CC0603KRX7R9BB104

**Facts this rule rests on:** each is published in full on the record page that owns it, at the anchor linked here.

- [`fact-c470643-resistance`](/docs/components/records/c470643/#fact-c470643-resistance) on RK10J11E0034
- [`fact-c470643-tolerance`](/docs/components/records/c470643/#fact-c470643-tolerance) on RK10J11E0034
- [`fact-c470643-terminals`](/docs/components/records/c470643/#fact-c470643-terminals) on RK10J11E0034
- [`fact-c470643-stops`](/docs/components/records/c470643/#fact-c470643-stops) on RK10J11E0034
- [`fact-c470643-project-nets`](/docs/components/records/c470643/#fact-c470643-project-nets) on RK10J11E0034
- [`fact-c470643-adc-design`](/docs/components/records/c470643/#fact-c470643-adc-design) on RK10J11E0034
- [`fact-c470643-firmware-target`](/docs/components/records/c470643/#fact-c470643-firmware-target) on RK10J11E0034
- [`fact-c529334-adc`](/docs/components/records/c529334/#fact-c529334-adc) on STM32G031F8P6
- [`fact-c529334-topology`](/docs/components/records/c529334/#fact-c529334-topology) on STM32G031F8P6
- [`fact-c22775-brightness-topology`](/docs/components/records/c22775/#fact-c22775-brightness-topology) on 0603WAF1000T5E
- [`fact-c25803-resistance`](/docs/components/records/c25803/#fact-c25803-resistance) on 0603WAF1003T5E
- [`fact-c14663-capacitance`](/docs/components/records/c14663/#fact-c14663-capacitance) on CC0603KRX7R9BB104

**Conditioned calculations:** none are recorded for this rule.

## Legend

What the recorded terms on this page mean, in ordinary words. The exact terms above are the ones that count; these descriptions explain them and never replace them.

### Rule verdict

| Recorded term | What it means |
| --- | --- |
| NEEDS BENCH | Cannot be settled from documents. It needs measurement on real hardware before it can be relied on. |
| UNSOURCED | No accepted source backs this value yet. Treat it as a claim, not a fact. |

### Domain

| Recorded term | What it means |
| --- | --- |
| al8860-led-stage | How the LED driver, its sense resistor, inductor, catch diode and per-branch ballast behave together across the LED forward-voltage, tolerance and temperature envelope. |
| ap63203-logic-stage | How the logic-rail converter, its inductor and its output capacitor behave together under the real load the microcontroller presents. |
| board-mounted lamp power switching | No plain-language description is recorded for this term yet. |
| ntc-adc-firmware | How the thermistor, its divider, the analog-to-digital input and the firmware that reads them combine into a temperature the design can act on. |
| potentiometer-brightness-adc | No plain-language description is recorded for this term yet. |
| rail-envelope | Whether every part on the input rail stays inside its own recorded limits across a legal power contract, a mis-contract, and a transient clamp event. |
| source-to-bench-chain | How far each claim has travelled from a manufacturer document towards a measurement on real hardware, stage by stage. |
| usb-pd-nvm-load-switch | How the power-delivery controller's stored configuration and its enable output drive the load switch, through every state from detached to fault. |

### Evidence stage

| Recorded term | What it means |
| --- | --- |
| as-built | The assembled board has been inspected and matches what was specified. |
| bench | The behaviour has been measured on powered hardware. |
| bom-cpl | The exact orderable part and its placement are confirmed in the assembly files.  |
| conditioned-requirement | The claim has been restated as a requirement with the conditions it holds under. |
| generated-netlist | The requirement is reflected in the netlist the project generates. |
| official-source | The claim appears in a document the manufacturer published. |
| pcb-orientation | The part's orientation and pad mapping are confirmed on the board layout. |
| programmed | The device's stored configuration has been written and read back. |
| symbol-footprint | The schematic symbol's pins are mapped onto the footprint's pads. |

### Evidence stage status

| Recorded term | What it means |
| --- | --- |
| MIXED | Some claims at this stage are settled and others are not. It is not a completed stage, and the facts listed against it are the ones that carry it. |
| OPEN | Nothing at this stage has been established yet. A completed earlier stage does not imply it. |

## Raw agent resource

These rules are generated from a stored evidence bundle and do not restate it. The bundle is the source of truth: where the two ever disagree, the bundle is right and this page is stale.

- [Open the owning bundle](/docs/claude-skills/circuit-spec-integration/) `circuit-spec-integration`
