Takazudo/zudo-led-lamp/doc/src/content/docs/claude-skills/component-gswitch-ss-12d01-g020/index.mdx

---
title: component-gswitch-ss-12d01-g020
description: Use to audit exact SS-12D01-G020 C5446803 low-profile maintained power slider, manufacturer evidence, JLCPCB sourcing, PCB pin mapping and prototype requirements.
sidebar_label: component-gswitch-ss-12d01-g020
generated: true
---

# SS-12D01-G020 low-profile maintained power slider

Run component-spec-audit first and read every JSON file in this owner. Use circuit-spec-integration for cross-component behavior. The exact part is fitted on Board L and sourced through JLCPCB; supplier stock is a dated observation, not a reservation or assembled-board proof.

SW2 is non-shorting SPDT. The reviewed project pin convention uses center 2 for fused input, outer 1 for V15, and outer 3 without a PCB net; terminal 3 is internally live in OFF. The manufacturer drawing is unnumbered and distributor-mirrored. G020 means 2 mm actuator projection above the 3.5 mm body; a generic 8 mm model is not the exact variant. Retain mirror-trust, inrush/contact-life and physical OFF/back-power gates.

## Human component reference

Generated [C5446803 record](/docs/components/records/c5446803/), [catalog](/docs/components/catalog/) and [integration](/docs/components/integration/). JSON evidence remains authoritative.
