Takazudo/zudo-led-lamp/doc/src/content/docs/claude-skills/component-type-c-31-m-17/index.mdx

---
title: component-type-c-31-m-17
description: Audit the exact HRO TYPE-C-31-M-17 C283540 USB-C receptacle. Use for Board P J1 contacts, shell, duplicate pads, orientation, footprint, ratings, bring-up, or substitution.
sidebar_label: component-type-c-31-m-17
generated: true
---

# TYPE-C-31-M-17

Run the central validator and read every local artifact. The official HRO page and Rev A drawing confirm the exact MPN, current/voltage, dielectric, insulation, contact-resistance, durability, temperature, and mechanical facts; the stable distributor mirror binds C283540. Reject Korean Hroparts Elec and other vendor substitutions. Do not promote the older mirror's superseded 3,000-cycle value or the conflicting +85 °C locale claim.

The primary contact sketch does not by itself prove the project's numeric symbol-to-pad mapping. Before assembly, mechanically compare the incoming part against pad centers, shell tabs, board edge, mating face, and orientation. Before PD, continuity-map both VBUS contacts, both grounds, CC1, CC2, and shell with no cable and both plug orientations.

## Human component reference

Human projection of this bundle: [rec-type-c-31-m-17](/docs/components/records/type-c-31-m-17/). Those pages are generated from the JSON files here and add nothing to them — where the two disagree, this bundle is correct. See also the [component catalog](/docs/components/catalog/) and the [cross-component rules](/docs/components/integration/).
