Takazudo/zudo-led-lamp/doc/src/content/docs/claude-skills/component-xfcn-board-headers/index.mdx

---
title: component-xfcn-board-headers
description: Audit the exact XFCN PZ254V-11-06P C492405 male and PM254V-11-06-H85 C2832269 female six-position 2.54 mm board-to-board headers. Use for Boards P/L pin order, orientation, footprint, ratings, mating,...
sidebar_label: component-xfcn-board-headers
generated: true
---

# XFCN 2.54 mm board-to-board headers

Run the central validator and read every local artifact. Board P JOUT1 is the male PZ254V-11-06P; Board L J2 is the female PM254V-11-06-H85. The manufacturer drawings explicitly specify the reciprocal PZ254/PM254 single-row series as mates.

The parts are unkeyed. Before powering mated boards, verify both PCB pin-1 marks, the physical board-to-board orientation, the six-net end-to-end map, standoff/alignment, full seating, and mechanical retention. The catalog mating statement does not prove the current PCB placements or enclosure mechanics.

## Human component reference

Human projections of this bundle: [PZ254V-11-06P](/docs/components/records/c492405/) and [PM254V-11-06-H85](/docs/components/records/c2832269/). Those pages are generated from the JSON files here and add nothing to them — where the two disagree, this bundle is correct. See also the [component catalog](/docs/components/catalog/) and the [cross-component rules](/docs/components/integration/).
