Takazudo/zudo-led-lamp/doc/src/content/docs/components/records/index.mdx

---
# GENERATED by doc/component-docs — do not edit; run `pnpm generate:components`
title: "Records"
description: "Per-record evidence pages: facts, sources, coverage domains, pin maps and interactions."
sidebar_position: 3
---

One page per published component record, each carrying that record's facts, sources, coverage domains, pin maps and interactions. They are ordered as the bill of materials orders them, with each subordinate record directly after the part it belongs to.

To compare records against each other, start from the [catalog](/docs/components/catalog/).

## Records

- [TYPE-C-31-M-17](/docs/components/records/type-c-31-m-17/) — `rec-type-c-31-m-17` USB-C receptacle
- [STUSB4500QTR](/docs/components/records/stusb4500qtr/) — `rec-stusb4500qtr` USB-PD sink controller
- [PESD24VS1UB,115](/docs/components/records/pesd24vs1ub/) — `rec-pesd24vs1ub` CC-line ESD protection
- [0603WAF5101T5E](/docs/components/records/rd-0603waf5101t5e/) — `rec-rd-0603waf5101t5e` external USB-C Rd resistor
- [AO3401A](/docs/components/records/umw-ao3401a/) — `rec-umw-ao3401a` P-channel load-switch MOSFET
- [SMAJ20A](/docs/components/records/high-diode-smaj20a/) — `rec-high-diode-smaj20a` 20 V TVS diode
- [CL31A106KBHNNNE](/docs/components/records/c13585/) — `rec-c13585` 10 uF 50 V MLCC
- [CC0603KRX7R9BB104](/docs/components/records/c14663/) — `rec-c14663` 100 nF 50 V MLCC
- [CL10A105KB8NNNC](/docs/components/records/c15849/) — `rec-c15849` 1 uF 50 V MLCC
- [0603WAF1003T5E](/docs/components/records/c25803/) — `rec-c25803` 100 kOhm resistor
- [0603WAF1503T5E](/docs/components/records/c22807/) — `rec-c22807` 150 kOhm resistor
- [0603WAF4700T5E](/docs/components/records/c23179/) — `rec-c23179` 470 Ohm resistor
- [0603WAF4701T5E](/docs/components/records/c23162/) — `rec-c23162` 4.7 kOhm resistor
- [0603WAF0000T5E](/docs/components/records/c21189/) — `rec-c21189` zero-Ohm CCDB bridge
- [0805W8F1002T5E](/docs/components/records/c17414/) — `rec-c17414` 10 kOhm resistor
- [PZ254V-11-06P](/docs/components/records/c492405/) — `rec-c492405` male board-to-board header
- [PM254V-11-06-H85](/docs/components/records/c2832269/) — `rec-c2832269` female board-to-board header
- [BSMD1206-075-30V](/docs/components/records/bsmd1206-075-30v/) — `rec-bsmd1206-075-30v` 750 mA PPTC fuse
- [AL8860MP-13](/docs/components/records/al8860mp-13/) — `rec-al8860mp-13` buck LED driver
- [RLP25FEER200](/docs/components/records/rlp25feer200/) — `rec-rlp25feer200` 200 mOhm current-sense resistor
- [FXL0630-330-M](/docs/components/records/fxl0630-330-m/) — `rec-fxl0630-330-m` 33 uH LED buck inductor
- [SS26](/docs/components/records/ro-ss26/) — `rec-ro-ss26` 60 V Schottky catch diode
- [AP63203WU-7](/docs/components/records/ap63203wu-7/) — `rec-ap63203wu-7` 3.3 V synchronous buck converter
- [FNR4030S4R7MT](/docs/components/records/fnr4030s4r7mt/) — `rec-fnr4030s4r7mt` 4.7 uH logic buck inductor
- [CL21A226MAQNNNE](/docs/components/records/cl21a226maqnnne/) — `rec-cl21a226maqnnne` 22 uF 25 V buck output MLCC
- [STM32G031F8P6](/docs/components/records/c529334/) — `rec-c529334` control MCU
- [PZ254V-11-05P](/docs/components/records/c492404/) — `rec-c492404` hand-fit SWD header
- [DS254P-2X10-L0](/docs/components/records/c4749199/) — `rec-c4749199` ST-LINK/V2 20-pin adapter header
- [RK10J11E0034](/docs/components/records/c470643/) — `rec-c470643` stopped brightness potentiometer
- [NCP18XH103F03RB](/docs/components/records/c13564/) — `rec-c13564` 10 kOhm NTC thermistor
- [0603WAF3302T5E](/docs/components/records/c4216/) — `rec-c4216` 33 kOhm resistor
- [0603WAF1000T5E](/docs/components/records/c22775/) — `rec-c22775` 100 Ohm brightness ADC series resistor
- [HL-AM-2835H421W-S1-08-HR3](/docs/components/records/c210315/) — `rec-c210315` 3000 K 2835 LED
- [FRC2512F33R0TS](/docs/components/records/c2934070/) — `rec-c2934070` 33 Ohm LED ballast resistor
- [SS-12D01-G020](/docs/components/records/c5446803/) — `rec-c5446803` maintained lamp power slider
