Takazudo/zudo-led-lamp/doc/src/content/docs/components/records/al8860mp-13/index.mdx

---
# GENERATED by doc/component-docs — do not edit; run `pnpm generate:components`
title: "AL8860MP-13"
description: "buck LED driver — Diodes Incorporated — C500782 — board-l U2 — rec-al8860mp-13"
sidebar_position: 20
---

<EvidenceAnchor id="rec-al8860mp-13" />

Everything below is projected from this project's stored component evidence. Values keep the exact wording, conditions, units and verdicts they were recorded with — nothing here is re-typed, corrected, or combined into an overall judgement about the part.

This record in the catalog: [AL8860MP-13](/docs/components/catalog/#rec-al8860mp-13)

## Identity

| Field | Recorded value |
| --- | --- |
| Record ID | `rec-al8860mp-13` |
| Record kind | standalone |
| Manufacturer part number | `AL8860MP-13` |
| Manufacturer | Diodes Incorporated |
| Function | buck LED driver |
| LCSC ID | `C500782` |
| Package | `MSOP-8_L3.0-W3.0-P0.65-LS4.9-BL-EP1.8` |
| Inventory line | `line-c500782` |
| Also known as | `hysteretic LED driver` |
| Owner skill | `component-al8860mp-13` |

**Fit:** Fitted

**Identity state:** UNRESOLVED

**Source state:** SOURCE UNAVAILABLE

**Coverage:** 1 open of 4 published

## Documents and package

<EvidenceAnchor id="component-references-heading" />

<ComponentReferences descriptor="7b2276657273696f6e223a312c22646f63756d656e74223a7b226c6162656c223a2244617461736865657420504446222c227469746c65223a22414c383836302034305620312e3541204275636b204c454420447269766572222c22617574686f72697479223a224d414e5546414354555245525f5052494d415259222c22617661696c6162696c697479223a22415641494c41424c45222c2275726c223a2268747470733a2f2f7777772e64696f6465732e636f6d2f6461746173686565742f646f776e6c6f61642f414c383836302e706466227d2c22666f6f747072696e74223a7b226e616d65223a224d534f502d385f4c332e302d57332e302d50302e36352d4c53342e392d424c2d4550312e38222c22617373657455726c223a222f6173736574732f636f6d706f6e656e742d70726576696577732f666f6f747072696e74732f4d534f502d385f4c332e302d57332e302d50302e36352d4c53342e392d424c2d4550312e382e737667227d2c226d6f64656c44657363726970746f72223a22376232323736363537323733363936663665323233613331326332323730363136333662363136373635343936343232336132323464353334663530326433383566346333333265333032643537333332653330326435303330326533363335326434633533333432653339326434323463326434353530333132653338323232633232373036313633366236313637363534633631363236353663323233613232346435333466353032643338356634633333326533303264353733333265333032643530333032653336333532643463353333343265333932643432346332643435353033313265333832323263323236643666363436353663353537323663323233613232326636313733373336353734373332663633366636643730366636653635366537343264373037323635373636393635373737333266366436663634363536633733326634643533346635303264333835663463333332653330326435373333326533303264353033303265333633353264346335333334326533393264343234633264343535303331326533383265373737323663323232633232366636363636373336353734323233613762323237383232336133303263323237393232336133303263323237613232336133303764326332323732366637343631373436393666366532323361376232323738323233613330326332323739323233613330326332323761323233613330376432633232373336333631366336353232336137623232373832323361333132633232373932323361333132633232376132323361333137643764227d" />

**Selected document:** [Datasheet PDF](https://www.diodes.com/datasheet/download/AL8860.pdf) — AL8860 40V 1.5A Buck LED Driver

**Selected source ID:** `src-al8860-ds39014`

**Authority:** MANUFACTURER\_PRIMARY

**Availability:** AVAILABLE

**Package footprint:** `MSOP-8_L3.0-W3.0-P0.65-LS4.9-BL-EP1.8`

This geometry represents a shared footprint package and may not exactly match the manufacturer part.

## Placements

Every position this exact line occupies in the as-built design. One line may be placed many times and across more than one board.

| Board | Reference designator |
| --- | --- |
| board-l | `U2` |

## Coverage

Coverage is stated one domain at a time and is never rolled up. A domain marked open is a question that has not been answered; it is not a finding that the part is unsuitable. A record with no open domains has not thereby been declared safe.

### pin-topology-and-ep

<EvidenceAnchor id="cov-al8860-pin-topology" />

**Coverage ID:** `cov-al8860-pin-topology` · **Status:** COVERED

**Reason:** fact-al8860-topology, fact-al8860-pin-ep, fact-al8860-project-nets

**Facts in this domain:**

- [`fact-al8860-topology`](#fact-al8860-topology)
- [`fact-al8860-pin-ep`](#fact-al8860-pin-ep)
- [`fact-al8860-project-nets`](#fact-al8860-project-nets)

### limits-control-timing-faults

<EvidenceAnchor id="cov-al8860-limits-control" />

**Coverage ID:** `cov-al8860-limits-control` · **Status:** COVERED

**Reason:** fact-al8860-vin-recommended-max through fact-al8860-faults, plus fact-al8860-duty-band (DS39014 Rev 8-2, Electrical Characteristics table row DSW Recommended Duty Cycle Range, re-verified 2026-08-02 against the currently live diodes.com PDF, hash-matched to the retained mirror)

**Facts in this domain:**

- [`fact-al8860-vin-recommended-max`](#fact-al8860-vin-recommended-max)
- [`fact-al8860-vin-absolute-max`](#fact-al8860-vin-absolute-max)
- [`fact-al8860-sense-min`](#fact-al8860-sense-min)
- [`fact-al8860-sense-max`](#fact-al8860-sense-max)
- [`fact-al8860-current-min`](#fact-al8860-current-min)
- [`fact-al8860-current-max`](#fact-al8860-current-max)
- [`fact-al8860-ripple-fraction`](#fact-al8860-ripple-fraction)
- [`fact-al8860-peak-current`](#fact-al8860-peak-current)
- [`fact-al8860-ctrl`](#fact-al8860-ctrl)
- [`fact-al8860-min-on-time`](#fact-al8860-min-on-time)
- [`fact-al8860-max-frequency`](#fact-al8860-max-frequency)
- [`fact-al8860-inductance-min`](#fact-al8860-inductance-min)
- [`fact-al8860-inductance-max`](#fact-al8860-inductance-max)
- [`fact-al8860-faults`](#fact-al8860-faults)
- [`fact-al8860-duty-band`](#fact-al8860-duty-band)

### layout-and-thermal

<EvidenceAnchor id="cov-al8860-layout" />

**Coverage ID:** `cov-al8860-layout` · **Status:** COVERED

**Reason:** fact-al8860-layout

**Facts in this domain:**

- [`fact-al8860-layout`](#fact-al8860-layout)

### led-string-voltage-temperature

<EvidenceAnchor id="cov-al8860-led-domain" />

**Coverage ID:** `cov-al8860-led-domain` · **Status:** OPEN

**Reason:** Exact LED VF versus current/temperature and switching-node overshoot require the LED/integration records and bench waveform.

**Facts in this domain:** none are recorded against it.

**Blocked by:** no blocking fact is recorded. What is missing has not been reduced to a specific recorded fact, so the reason above is the whole of what is known.

## Facts

Each fact keeps its value, its unit, the conditions it holds under, where it came from and how far it has been confirmed as separate fields, because they are separate claims. A value without its conditions is not the same fact, and a verdict is about the evidence for the value, not about the part.

### ABSOLUTE\_MAXIMUM

A never-exceed limit. Reaching it may damage the part; it is not an operating target and there is no margin implied by it.

<EvidenceFact>
  <EvidenceAnchor id="fact-al8860-vin-absolute-max" />

  **Fact:** `fact-al8860-vin-absolute-max`

  **Value:** 42 · **Unit:** `V`

  **Conditions:** stress rating only, TA=25 C

  **Verdict:** PASS - primary-source confirmed · **Provenance:** PRIMARY-SPEC

  **Evidence:** [src-al8860-ds39014: Absolute Maximum Ratings table row VIN](#src-al8860-ds39014)
</EvidenceFact>

### RECOMMENDED\_OPERATION

The range the manufacturer intends the part to be used in. Always narrower than the absolute maximum.

<EvidenceFact>
  <EvidenceAnchor id="fact-al8860-topology" />

  **Fact:** `fact-al8860-topology`

  **Value:** hysteretic buck LED driver with integrated NDMOS and high-side current sense · **Unit:** `NONE`

  **Conditions:** normal buck operation

  **Verdict:** PASS - primary-source confirmed · **Provenance:** PRIMARY-SPEC

  **Evidence:** [src-al8860-ds39014: Section Application Information and Figure Typical Application Circuit](#src-al8860-ds39014)
</EvidenceFact>

<EvidenceFact>
  <EvidenceAnchor id="fact-al8860-pin-ep" />

  **Fact:** `fact-al8860-pin-ep`

  **Value:** EP connects to GND thermal mass but is not an electrical ground conduction path · **Unit:** `NONE`

  **Conditions:** MSOP-8EP package

  **Verdict:** PASS - primary-source confirmed · **Provenance:** PRIMARY-SPEC

  **Evidence:** [src-al8860-ds39014: Pin Descriptions table row EP](#src-al8860-ds39014)
</EvidenceFact>

<EvidenceFact>
  <EvidenceAnchor id="fact-al8860-vin-recommended-max" />

  **Fact:** `fact-al8860-vin-recommended-max`

  **Value:** 40 · **Unit:** `V`

  **Conditions:** functional input range, TA=25 C unless specified

  **Verdict:** PASS - primary-source confirmed · **Provenance:** PRIMARY-SPEC

  **Evidence:** [src-al8860-ds39014: Recommended Operating Conditions table row VIN](#src-al8860-ds39014)
</EvidenceFact>

<EvidenceFact>
  <EvidenceAnchor id="fact-al8860-ctrl" />

  **Fact:** `fact-al8860-ctrl`

  **Value:** floating gives normal operation; below 0.2 V disables; 0.3-2.5 V analog dims; PWM below 500 Hz preserves best range · **Unit:** `NONE`

  **Conditions:** CTRL pin operation

  **Verdict:** PASS - primary-source confirmed · **Provenance:** PRIMARY-SPEC

  **Evidence:** [src-al8860-ds39014: Pin Descriptions table row CTRL and Application Information section PWM Dimming](#src-al8860-ds39014)
</EvidenceFact>

<EvidenceFact>
  <EvidenceAnchor id="fact-al8860-min-on-time" />

  **Fact:** `fact-al8860-min-on-time`

  **Value:** 500 · **Unit:** `ns`

  **Conditions:** recommended minimum switch on-time for 4% accuracy

  **Verdict:** PASS - primary-source confirmed · **Provenance:** PRIMARY-SPEC

  **Evidence:** [src-al8860-ds39014: Electrical Characteristics table row tON\_REC](#src-al8860-ds39014)
</EvidenceFact>

<EvidenceFact>
  <EvidenceAnchor id="fact-al8860-max-frequency" />

  **Fact:** `fact-al8860-max-frequency`

  **Value:** 1 · **Unit:** `MHz`

  **Conditions:** recommended maximum switch frequency

  **Verdict:** PASS - primary-source confirmed · **Provenance:** PRIMARY-SPEC

  **Evidence:** [src-al8860-ds39014: Electrical Characteristics table row fSW(MAX)](#src-al8860-ds39014)
</EvidenceFact>

<EvidenceFact>
  <EvidenceAnchor id="fact-al8860-inductance-min" />

  **Fact:** `fact-al8860-inductance-min`

  **Value:** 33 · **Unit:** `uH`

  **Conditions:** recommended AL8860 inductor range

  **Verdict:** PASS - primary-source confirmed · **Provenance:** PRIMARY-SPEC

  **Evidence:** [src-al8860-ds39014: Section Inductor Selection row recommended range](#src-al8860-ds39014)
</EvidenceFact>

<EvidenceFact>
  <EvidenceAnchor id="fact-al8860-inductance-max" />

  **Fact:** `fact-al8860-inductance-max`

  **Value:** 100 · **Unit:** `uH`

  **Conditions:** recommended AL8860 inductor range

  **Verdict:** PASS - primary-source confirmed · **Provenance:** PRIMARY-SPEC

  **Evidence:** [src-al8860-ds39014: Section Inductor Selection row recommended range](#src-al8860-ds39014)
</EvidenceFact>

<EvidenceFact>
  <EvidenceAnchor id="fact-al8860-faults" />

  **Fact:** `fact-al8860-faults`

  **Value:** open LED stops oscillation; shorted LED chain remains regulated but changes duty and frequency; OTP restarts after hysteresis · **Unit:** `NONE`

  **Conditions:** documented open, short, and overtemperature states

  **Verdict:** PASS - primary-source confirmed · **Provenance:** PRIMARY-SPEC

  **Evidence:** [src-al8860-ds39014: Sections Thermal Protection, Open Circuit LEDs, and LED Chain Shorted Together](#src-al8860-ds39014)
</EvidenceFact>

<EvidenceFact>
  <EvidenceAnchor id="fact-al8860-duty-band" />

  **Fact:** `fact-al8860-duty-band`

  **Value:** 25 to 75 · **Unit:** `%`

  **Conditions:** DSW parameter, internal buck-switch operating duty-cycle recommended range, guaranteed by design; distinct from the 98% DSW(MAX) absolute maximum duty cycle and from the 5-100% CTRL-pin analog-dimming range

  **Verdict:** PASS - primary-source confirmed · **Provenance:** PRIMARY-SPEC

  **Evidence:** [src-al8860-ds39014: Electrical Characteristics table row DSW Recommended Duty Cycle Range](#src-al8860-ds39014)
</EvidenceFact>

### GUARANTEED\_ELECTRICAL

A parameter the manufacturer guarantees over the stated conditions, usually with minimum, typical and maximum values.

<EvidenceFact>
  <EvidenceAnchor id="fact-al8860-sense-min" />

  **Fact:** `fact-al8860-sense-min`

  **Value:** 0.096 · **Unit:** `V`

  **Conditions:** SET relative to VIN, TA=25 C unless specified

  **Verdict:** PASS - primary-source confirmed · **Provenance:** PRIMARY-SPEC

  **Evidence:** [src-al8860-ds39014: Electrical Characteristics table row VSENSE minimum](#src-al8860-ds39014)
</EvidenceFact>

<EvidenceFact>
  <EvidenceAnchor id="fact-al8860-sense-max" />

  **Fact:** `fact-al8860-sense-max`

  **Value:** 0.104 · **Unit:** `V`

  **Conditions:** SET relative to VIN, TA=25 C unless specified

  **Verdict:** PASS - primary-source confirmed · **Provenance:** PRIMARY-SPEC

  **Evidence:** [src-al8860-ds39014: Electrical Characteristics table row VSENSE maximum](#src-al8860-ds39014)
</EvidenceFact>

<EvidenceFact>
  <EvidenceAnchor id="fact-al8860-ripple-fraction" />

  **Fact:** `fact-al8860-ripple-fraction`

  **Value:** 0.4 · **Unit:** `ratio`

  **Conditions:** internally set coil peak-to-peak ripple relative to ILED

  **Verdict:** PASS - primary-source confirmed · **Provenance:** PRIMARY-SPEC

  **Evidence:** [src-al8860-ds39014: Section Inductor Selection equation definitions row delta-I](#src-al8860-ds39014)
</EvidenceFact>

### THERMAL\_SOA

Thermal and safe-operating-area behaviour: how much the part may dissipate, and under what mounting and ambient conditions.

<EvidenceFact>
  <EvidenceAnchor id="fact-al8860-layout" />

  **Fact:** `fact-al8860-layout`

  **Value:** place input capacitor and inductor close; use low-resistance SW path; connect EP to thermal mass · **Unit:** `NONE`

  **Conditions:** MSOP-8EP implementation

  **Verdict:** PASS - primary-source confirmed · **Provenance:** PRIMARY-SPEC

  **Evidence:** [src-al8860-ds39014: Pin Descriptions table row EP and Sections Capacitor Selection and Inductor Selection](#src-al8860-ds39014)
</EvidenceFact>

### PROJECT\_STATE

A value this project recorded about how the part is used here — a chosen operating point, a net assignment, or a derived figure. Not a manufacturer specification.

<EvidenceFact>
  <EvidenceAnchor id="fact-al8860-manufacturer" />

  **Fact:** `fact-al8860-manufacturer`

  **Value:** Diodes Incorporated · **Unit:** `NONE`

  **Conditions:** exact AL8860MP-13 orderable identity

  **Verdict:** PASS - primary-source confirmed · **Provenance:** PRIMARY-SPEC

  **Evidence:** [src-al8860-ds39014: title block and ordering table row AL8860MP-13](#src-al8860-ds39014)
</EvidenceFact>

<EvidenceFact>
  <EvidenceAnchor id="fact-al8860-current-min" />

  **Fact:** `fact-al8860-current-min`

  **Value:** 0.4752475247524752 · **Unit:** `A`

  **Conditions:** CTRL floating, minimum sense threshold and maximum initial sense resistance at 25 C; TCR and self-heating unresolved

  **Verdict:** NEEDS BENCH · **Provenance:** CALCULATED

  **Evidence:** [`src-al8860-ds39014`](#src-al8860-ds39014) — CALCULATED: fact-al8860-sense-min divided by fact-rlp25-resistance-max
</EvidenceFact>

<EvidenceFact>
  <EvidenceAnchor id="fact-al8860-current-max" />

  **Fact:** `fact-al8860-current-max`

  **Value:** 0.5252525252525252 · **Unit:** `A`

  **Conditions:** CTRL floating, maximum sense threshold and minimum initial sense resistance at 25 C; TCR and self-heating unresolved

  **Verdict:** NEEDS BENCH · **Provenance:** CALCULATED

  **Evidence:** [`src-al8860-ds39014`](#src-al8860-ds39014) — CALCULATED: fact-al8860-sense-max divided by fact-rlp25-resistance-min
</EvidenceFact>

<EvidenceFact>
  <EvidenceAnchor id="fact-al8860-peak-current" />

  **Fact:** `fact-al8860-peak-current`

  **Value:** 0.6303030303030303 · **Unit:** `A`

  **Conditions:** upper sense threshold, minimum initial 1% sense resistance, half of 40% peak-to-peak ripple above mean; TCR and self-heating unresolved

  **Verdict:** NEEDS BENCH · **Provenance:** CALCULATED

  **Evidence:** [`src-al8860-ds39014`](#src-al8860-ds39014) — CALCULATED: fact-al8860-current-max times one plus fact-al8860-ripple-fraction divided by two
</EvidenceFact>

<EvidenceFact>
  <EvidenceAnchor id="fact-al8860-project-nets" />

  **Fact:** `fact-al8860-project-nets`

  **Value:** U2.8=V15; U2.1=SET; U2.4=CTRL; U2.5/6=LED\_N; U2.2/3/9=GND; U2.7=NC · **Unit:** `NONE`

  **Conditions:** current generated Board L source

  **Verdict:** NOT APPLICABLE · **Provenance:** PROJECT-CHOICE

  **Evidence:** [src-al8860-generator: COMPONENTS table row U2, NETS rows, and NO\_CONNECT row U2.7](#src-al8860-generator)
</EvidenceFact>

## Calculation dependencies

These values were derived from other recorded facts rather than read from a document. The expression and every input are published so the number can be recomputed instead of trusted. A derived value is never stronger than the weakest fact it depends on.

**Fact:** [`fact-al8860-current-min`](#fact-al8860-current-min)

**Expression:** `fact_al8860_sense_min / fact_rlp25_resistance_max`

**Depends on:**

- [`fact-al8860-sense-min`](#fact-al8860-sense-min)
- [`fact-rlp25-resistance-max`](/docs/components/records/rlp25feer200/#fact-rlp25-resistance-max) on RLP25FEER200

**Fact:** [`fact-al8860-current-max`](#fact-al8860-current-max)

**Expression:** `fact_al8860_sense_max / fact_rlp25_resistance_min`

**Depends on:**

- [`fact-al8860-sense-max`](#fact-al8860-sense-max)
- [`fact-rlp25-resistance-min`](/docs/components/records/rlp25feer200/#fact-rlp25-resistance-min) on RLP25FEER200

**Fact:** [`fact-al8860-peak-current`](#fact-al8860-peak-current)

**Expression:** `fact_al8860_current_max * (1 + fact_al8860_ripple_fraction / 2)`

**Depends on:**

- [`fact-al8860-current-max`](#fact-al8860-current-max)
- [`fact-al8860-ripple-fraction`](#fact-al8860-ripple-fraction)

## Pin maps

The mapping between schematic pins and PCB pads, or physical terminals for an external part, as recorded. A record may carry more than one map when the same part is documented in more than one context.

### pinmap-al8860

<EvidenceAnchor id="pinmap-al8860" />

- **Symbol:** `AL8860MP-13`
- **Footprint:** `MSOP-8_L3.0-W3.0-P0.65-LS4.9-BL-EP1.8`
- **Pins:** 9

<EvidenceDetails label="pin-assignments">
  <EvidenceTable label="pin-assignments">
    | Symbol pin | Name   | Footprint pad | Function                                       |
    | ---------- | ------ | ------------- | ---------------------------------------------- |
    | `1`        | `SET`  | `1`           | sense input; Board L SET                       |
    | `2`        | `GND`  | `2`           | ground                                         |
    | `3`        | `GND`  | `3`           | ground                                         |
    | `4`        | `CTRL` | `4`           | PWM/analog control                             |
    | `5`        | `SW`   | `5`           | switch drain; LED\_N                           |
    | `6`        | `SW`   | `6`           | switch drain; LED\_N                           |
    | `7`        | `NC`   | `7`           | no connection                                  |
    | `8`        | `VIN`  | `8`           | V15 input                                      |
    | `9`        | `EP`   | `9`           | GND thermal pad, not current-return substitute |
  </EvidenceTable>
</EvidenceDetails>

## Interactions

Behaviour that is not a property of this part alone. Each interaction names the records it spans, the conditions it holds under, and how far it has been confirmed. An interaction that spans several parts appears on every one of their pages, under the same identifier, because it is equally a fact about each.

### int-al8860-control

<EvidenceAnchor id="int-al8860-control" />

- **Records involved:** `rec-al8860mp-13` (this record)
- **Conditions:** CTRL driven by Board L PWM\_DIM with analog/PWM state and frequency verified
- **Verdict:** NEEDS BENCH

**Facts this rests on:**

- [`fact-al8860-ctrl`](#fact-al8860-ctrl)
- [`fact-al8860-min-on-time`](#fact-al8860-min-on-time)
- [`fact-al8860-max-frequency`](#fact-al8860-max-frequency)
- [`fact-al8860-project-nets`](#fact-al8860-project-nets)

### int-al8860-power-stage

<EvidenceAnchor id="int-al8860-power-stage" />

- **Records involved:** `rec-al8860mp-13` (this record), [`rec-rlp25feer200`](/docs/components/records/rlp25feer200/), [`rec-fxl0630-330-m`](/docs/components/records/fxl0630-330-m/), [`rec-ro-ss26`](/docs/components/records/ro-ss26/)
- **Conditions:** full LED-string VF/temperature, V15 transient, layout parasitics, and PWM operating envelope
- **Verdict:** NEEDS BENCH

**Facts this rests on:**

- [`fact-al8860-peak-current`](#fact-al8860-peak-current)
- [`fact-rlp25-power-margin`](/docs/components/records/rlp25feer200/#fact-rlp25-power-margin) on RLP25FEER200
- [`fact-fxl-isat-margin`](/docs/components/records/fxl0630-330-m/#fact-fxl-isat-margin) on FXL0630-330-M
- [`fact-ss26-voltage-margin`](/docs/components/records/ro-ss26/#fact-ss26-voltage-margin) on SS26
- [`fact-ss26-current-margin`](/docs/components/records/ro-ss26/#fact-ss26-current-margin) on SS26

## Cross-component rules

Rules that span several parts at once and are published in full on the integration page. Each rule's verdict below is that rule's own — it is a statement about the cross-component question, not about this part — and the exact wording of what the rule refuses to conclude is published with the rule itself.

- [`rule-rail-envelope`](/docs/components/integration/#rule-rail-envelope) — rail-envelope — **rule verdict:** UNSOURCED — Whether every part on the input rail stays inside its own recorded limits across a legal power contract, a mis-contract, and a transient clamp event.
- [`rule-usb-pd-nvm-load-switch`](/docs/components/integration/#rule-usb-pd-nvm-load-switch) — usb-pd-nvm-load-switch — **rule verdict:** UNSOURCED — How the power-delivery controller's stored configuration and its enable output drive the load switch, through every state from detached to fault.
- [`rule-al8860-led-stage`](/docs/components/integration/#rule-al8860-led-stage) — al8860-led-stage — **rule verdict:** NEEDS BENCH — How the LED driver, its sense resistor, inductor, catch diode and per-branch ballast behave together across the LED forward-voltage, tolerance and temperature envelope.
- [`rule-evidence-chain`](/docs/components/integration/#rule-evidence-chain) — source-to-bench-chain — **rule verdict:** NEEDS BENCH — How far each claim has travelled from a manufacturer document towards a measurement on real hardware, stage by stage.
- [`rule-c5446803-power-cut`](/docs/components/integration/#rule-c5446803-power-cut) — board-mounted lamp power switching — **rule verdict:** NEEDS BENCH

[All cross-component rules](/docs/components/integration/)

## Sources

Every document cited above, with its identification, when it was retrieved, and what kind of authority it carries. Sources that could not be retrieved are listed too, with their unavailability stated, so a gap in the evidence is visible rather than absent.

### AL8860 40V 1.5A Buck LED Driver

<EvidenceAnchor id="src-al8860-ds39014" />

**Source ID:** `src-al8860-ds39014` · **Authority:** MANUFACTURER\_PRIMARY

| Field | Recorded value |
| --- | --- |
| Document number | DS39014 |
| Revision | Rev. 8-2 |
| Document date | 2026-04 |
| Retrieved | 2026-08-02 |
| Printed page | 2 of 18 |

**Locator:** Pin Descriptions table; Absolute Maximum and Recommended Operating Conditions tables; Electrical Characteristics table; Application Information sections

**Availability:** AVAILABLE

**Document URL:** [https://www.diodes.com/datasheet/download/AL8860.pdf](https://www.diodes.com/datasheet/download/AL8860.pdf)

### Board L generated schematic specification

<EvidenceAnchor id="src-al8860-generator" />

**Source ID:** `src-al8860-generator` · **Authority:** PROJECT\_GENERATOR

| Field | Recorded value |
| --- | --- |
| Document number | scripts/schgen/board\_l\_spec.py |
| Revision | 410bc1a342286dd6c205d6dcec0f248b8a963987 |
| Document date | 2026-08-02 |
| Retrieved | 2026-08-02 |
| Printed page | source file |

**Locator:** COMPONENTS table row U2 and NETS rows V15, SET, LED\_N, CTRL, PWM\_DIM, and GND

**Availability:** AVAILABLE

**Document URL:** [https://raw.githubusercontent.com/Takazudo/zudo-led-lamp/410bc1a342286dd6c205d6dcec0f248b8a963987/scripts/schgen/board\_l\_spec.py](https://raw.githubusercontent.com/Takazudo/zudo-led-lamp/410bc1a342286dd6c205d6dcec0f248b8a963987/scripts/schgen/board_l_spec.py)

## Legend

What the recorded terms on this page mean, in ordinary words. The exact terms above are the ones that count; these descriptions explain them and never replace them.

### Verdict

| Recorded term | What it means |
| --- | --- |
| `NEEDS BENCH` | Cannot be settled from documents. It needs measurement on real hardware before it can be relied on. |
| `NOT APPLICABLE` | The parameter does not apply to this part as it is used here. |
| `PASS - primary-source confirmed` | Confirmed against the manufacturer's own document for this exact part. |

### Provenance

| Recorded term | What it means |
| --- | --- |
| `CALCULATED` | Derived arithmetically from other facts listed here. The expression and every input are shown, so the number can be recomputed rather than trusted. |
| `PRIMARY-SPEC` | Taken from the manufacturer's own specification document. |
| `PROJECT-CHOICE` | A decision made by this project. No vendor asserts it. |

### Fact class

| Recorded term | What it means |
| --- | --- |
| `ABSOLUTE_MAXIMUM` | A never-exceed limit. Reaching it may damage the part; it is not an operating target and there is no margin implied by it. |
| `GUARANTEED_ELECTRICAL` | A parameter the manufacturer guarantees over the stated conditions, usually with minimum, typical and maximum values. |
| `PROJECT_STATE` | A value this project recorded about how the part is used here — a chosen operating point, a net assignment, or a derived figure. Not a manufacturer specification. |
| `RECOMMENDED_OPERATION` | The range the manufacturer intends the part to be used in. Always narrower than the absolute maximum. |
| `THERMAL_SOA` | Thermal and safe-operating-area behaviour: how much the part may dissipate, and under what mounting and ambient conditions. |

### Coverage status

| Recorded term | What it means |
| --- | --- |
| `COVERED` | Every question this domain asks is answered by the facts listed against it. |
| `OPEN` | Unresolved. Open means the question has not been answered, not that the part is unsafe — the reason states what is missing. |

### Source availability

| Recorded term | What it means |
| --- | --- |
| `AVAILABLE` | The document was retrieved and is on record. |

### Source authority

| Recorded term | What it means |
| --- | --- |
| `MANUFACTURER_PRIMARY` | The manufacturer's own document for this exact part. |
| `PROJECT_GENERATOR` | A document this project generated, such as a schematic or netlist export. |

### Identity state

| Recorded term | What it means |
| --- | --- |
| `UNRESOLVED`  | The exact orderable part is not yet confirmed. Substituting a same-name part from another vendor is not permitted on that basis. |

### Source state

| Recorded term | What it means |
| --- | --- |
| `SOURCE UNAVAILABLE` | No document backing this line could be retrieved. |

### Unit

| Recorded term | What it means |
| --- | --- |
| `NONE` | The value is not a physical quantity, so it carries no unit. Recorded as \`NONE\`. |

## Raw agent resource

This page is generated from a stored evidence bundle and does not restate it. The bundle is the source of truth: where the two ever disagree, the bundle is right and this page is stale.

[Open the owning bundle](/docs/claude-skills/component-al8860mp-13/) `component-al8860mp-13`
