Takazudo/zudo-led-lamp/doc/src/content/docs/components/records/ap63203wu-7/index.mdx

---
# GENERATED by doc/component-docs — do not edit; run `pnpm generate:components`
title: "AP63203WU-7"
description: "3.3 V synchronous buck converter — Diodes Incorporated — C780769 — board-l U4 — rec-ap63203wu-7"
sidebar_position: 24
---

<EvidenceAnchor id="rec-ap63203wu-7" />

Everything below is projected from this project's stored component evidence. Values keep the exact wording, conditions, units and verdicts they were recorded with — nothing here is re-typed, corrected, or combined into an overall judgement about the part.

This record in the catalog: [AP63203WU-7](/docs/components/catalog/#rec-ap63203wu-7)

## Identity

| Field | Recorded value |
| --- | --- |
| Record ID | `rec-ap63203wu-7` |
| Record kind | standalone |
| Manufacturer part number | `AP63203WU-7` |
| Manufacturer | Diodes Incorporated |
| Function | 3.3 V synchronous buck converter |
| LCSC ID | `C780769` |
| Package | `TSOT-26_L2.9-W1.6-P0.95-LS2.8-BL` |
| Inventory line | `line-c780769` |
| Also known as | `logic buck` |
| Owner skill | `component-ap63203wu-7` |

**Fit:** Fitted

**Identity state:** UNRESOLVED

**Source state:** SOURCE UNAVAILABLE

**Coverage:** 2 open of 4 published

## Documents and package

<EvidenceAnchor id="component-references-heading" />

<ComponentReferences descriptor="7b2276657273696f6e223a312c22646f63756d656e74223a7b226c6162656c223a2244617461736865657420504446222c227469746c65223a22415036333230302f415036333230312f415036333230332f4150363332303520332e385620746f2033325620496e7075742032412053796e6368726f6e6f7573204275636b222c22617574686f72697479223a224d414e5546414354555245525f5052494d415259222c22617661696c6162696c697479223a22415641494c41424c45222c2275726c223a2268747470733a2f2f7777772e64696f6465732e636f6d2f6461746173686565742f646f776e6c6f61642f415036333230302d415036333230312d415036333230332d415036333230352e706466227d2c22666f6f747072696e74223a7b226e616d65223a2254534f542d32365f4c322e392d57312e362d50302e39352d4c53322e382d424c222c22617373657455726c223a222f6173736574732f636f6d706f6e656e742d70726576696577732f666f6f747072696e74732f54534f542d32365f4c322e392d57312e362d50302e39352d4c53322e382d424c2e737667227d2c226d6f64656c44657363726970746f72223a22376232323736363537323733363936663665323233613331326332323730363136333662363136373635343936343232336132323534353334663534326433323336356634633332326533393264353733313265333632643530333032653339333532643463353333323265333832643432346332323263323237303631363336623631363736353463363136323635366332323361323235343533346635343264333233363566346333323265333932643537333132653336326435303330326533393335326434633533333232653338326434323463323232633232366436663634363536633535373236633232336132323266363137333733363537343733326636333666366437303666366536353665373432643730373236353736363936353737373332663664366636343635366337333266353435333466353432643332333635663463333232653339326435373331326533363264353033303265333933353264346335333332326533383264343234633265373737323663323232633232366636363636373336353734323233613762323237383232336133303263323237393232336133303263323237613232336133303764326332323732366637343631373436393666366532323361376232323738323233613330326332323739323233613330326332323761323233613330376432633232373336333631366336353232336137623232373832323361333132633232373932323361333132633232376132323361333137643764227d" />

**Selected document:** [Datasheet PDF](https://www.diodes.com/datasheet/download/AP63200-AP63201-AP63203-AP63205.pdf) — AP63200/AP63201/AP63203/AP63205 3.8V to 32V Input 2A Synchronous Buck

**Selected source ID:** `src-ap6320x-ds41326`

**Authority:** MANUFACTURER\_PRIMARY

**Availability:** AVAILABLE

**Package footprint:** `TSOT-26_L2.9-W1.6-P0.95-LS2.8-BL`

This geometry represents a shared footprint package and may not exactly match the manufacturer part.

## Placements

Every position this exact line occupies in the as-built design. One line may be placed many times and across more than one board.

| Board | Reference designator |
| --- | --- |
| board-l | `U4` |

## Coverage

Coverage is stated one domain at a time and is never rolled up. A domain marked open is a question that has not been answered; it is not a finding that the part is unsuitable. A record with no open domains has not thereby been declared safe.

### topology-pins-limits-startup-faults

<EvidenceAnchor id="cov-ap63203-core" />

**Coverage ID:** `cov-ap63203-core` · **Status:** COVERED

**Reason:** fact-ap63203-topology through fact-ap63203-hiccup and fact-ap63203-project-nets

**Facts in this domain:**

- [`fact-ap63203-topology`](#fact-ap63203-topology)
- [`fact-ap63203-en-open`](#fact-ap63203-en-open)
- [`fact-ap63203-vin-recommended-max`](#fact-ap63203-vin-recommended-max)
- [`fact-ap63203-vin-absolute-dc`](#fact-ap63203-vin-absolute-dc)
- [`fact-ap63203-vin-transient`](#fact-ap63203-vin-transient)
- [`fact-ap63203-vout-min`](#fact-ap63203-vout-min)
- [`fact-ap63203-vout-max`](#fact-ap63203-vout-max)
- [`fact-ap63203-frequency`](#fact-ap63203-frequency)
- [`fact-ap63203-min-on-time`](#fact-ap63203-min-on-time)
- [`fact-ap63203-soft-start`](#fact-ap63203-soft-start)
- [`fact-ap63203-peak-limit-min`](#fact-ap63203-peak-limit-min)
- [`fact-ap63203-hiccup`](#fact-ap63203-hiccup)

### lc-envelope-compensation-and-layout

<EvidenceAnchor id="cov-ap63203-lc" />

**Coverage ID:** `cov-ap63203-lc` · **Status:** COVERED

**Reason:** fact-ap63203-inductor-min through fact-ap63203-layout

**Facts in this domain:**

- [`fact-ap63203-inductor-min`](#fact-ap63203-inductor-min)
- [`fact-ap63203-inductor-max`](#fact-ap63203-inductor-max)
- [`fact-ap63203-load-max`](#fact-ap63203-load-max)
- [`fact-ap63203-current-headroom`](#fact-ap63203-current-headroom)
- [`fact-ap63203-required-inductor-current`](#fact-ap63203-required-inductor-current)
- [`fact-ap63203-dcr-max`](#fact-ap63203-dcr-max)
- [`fact-ap63203-cap-min`](#fact-ap63203-cap-min)
- [`fact-ap63203-cap-max`](#fact-ap63203-cap-max)
- [`fact-ap63203-reference-l`](#fact-ap63203-reference-l)
- [`fact-ap63203-reference-cap`](#fact-ap63203-reference-cap)
- [`fact-ap63203-thermal`](#fact-ap63203-thermal)
- [`fact-ap63203-layout`](#fact-ap63203-layout)

### minimum-off-time

<EvidenceAnchor id="cov-ap63203-off" />

**Coverage ID:** `cov-ap63203-off` · **Status:** OPEN

**Reason:** DS41326 gives 80 ns minimum on-time but no minimum off-time; the 220 ns bootstrap refresh interval is a different behavior.

**Facts in this domain:** none are recorded against it.

**Blocked by:** no blocking fact is recorded. What is missing has not been reduced to a specific recorded fact, so the reason above is the whole of what is known.

### project-load-transients-and-thermal

<EvidenceAnchor id="cov-ap63203-load" />

**Coverage ID:** `cov-ap63203-load` · **Status:** OPEN

**Reason:** The generated source does not bound V3P3 load steps, sustained load, copper thermal impedance, or V15 transients.

**Facts in this domain:** none are recorded against it.

**Blocked by:** no blocking fact is recorded. What is missing has not been reduced to a specific recorded fact, so the reason above is the whole of what is known.

## Facts

Each fact keeps its value, its unit, the conditions it holds under, where it came from and how far it has been confirmed as separate fields, because they are separate claims. A value without its conditions is not the same fact, and a verdict is about the evidence for the value, not about the part.

### ABSOLUTE\_MAXIMUM

A never-exceed limit. Reaching it may damage the part; it is not an operating target and there is no margin implied by it.

<EvidenceFact>
  <EvidenceAnchor id="fact-ap63203-vin-absolute-dc" />

  **Fact:** `fact-ap63203-vin-absolute-dc`

  **Value:** 35 · **Unit:** `V`

  **Conditions:** DC stress rating only

  **Verdict:** PASS - primary-source confirmed · **Provenance:** PRIMARY-SPEC

  **Evidence:** [src-ap6320x-ds41326: Absolute Maximum Ratings table row VIN DC](#src-ap6320x-ds41326)
</EvidenceFact>

### RECOMMENDED\_OPERATION

The range the manufacturer intends the part to be used in. Always narrower than the absolute maximum.

<EvidenceFact>
  <EvidenceAnchor id="fact-ap63203-topology" />

  **Fact:** `fact-ap63203-topology`

  **Value:** fixed 3.3 V synchronous peak-current-mode buck with integrated compensation and PFM at light load · **Unit:** `NONE`

  **Conditions:** AP63203 variant

  **Verdict:** PASS - primary-source confirmed · **Provenance:** PRIMARY-SPEC

  **Evidence:** [src-ap6320x-ds41326: Features table rows AP63203 and Section PWM/PFM Operation](#src-ap6320x-ds41326)
</EvidenceFact>

<EvidenceFact>
  <EvidenceAnchor id="fact-ap63203-vin-recommended-max" />

  **Fact:** `fact-ap63203-vin-recommended-max`

  **Value:** 32 · **Unit:** `V`

  **Conditions:** functional input range

  **Verdict:** PASS - primary-source confirmed · **Provenance:** PRIMARY-SPEC

  **Evidence:** [src-ap6320x-ds41326: Recommended Operating Conditions table row VIN](#src-ap6320x-ds41326)
</EvidenceFact>

<EvidenceFact>
  <EvidenceAnchor id="fact-ap63203-inductor-min" />

  **Fact:** `fact-ap63203-inductor-min`

  **Value:** 2.2 · **Unit:** `uH`

  **Conditions:** general recommended inductor envelope

  **Verdict:** PASS - primary-source confirmed · **Provenance:** PRIMARY-SPEC

  **Evidence:** [src-ap6320x-ds41326: Section Inductor row recommended range](#src-ap6320x-ds41326)
</EvidenceFact>

<EvidenceFact>
  <EvidenceAnchor id="fact-ap63203-inductor-max" />

  **Fact:** `fact-ap63203-inductor-max`

  **Value:** 10 · **Unit:** `uH`

  **Conditions:** general recommended inductor envelope

  **Verdict:** PASS - primary-source confirmed · **Provenance:** PRIMARY-SPEC

  **Evidence:** [src-ap6320x-ds41326: Section Inductor row recommended range](#src-ap6320x-ds41326)
</EvidenceFact>

<EvidenceFact>
  <EvidenceAnchor id="fact-ap63203-load-max" />

  **Fact:** `fact-ap63203-load-max`

  **Value:** 2 · **Unit:** `A`

  **Conditions:** maximum continuous output design point

  **Verdict:** PASS - primary-source confirmed · **Provenance:** PRIMARY-SPEC

  **Evidence:** [src-ap6320x-ds41326: Features table row continuous output current](#src-ap6320x-ds41326)
</EvidenceFact>

<EvidenceFact>
  <EvidenceAnchor id="fact-ap63203-current-headroom" />

  **Fact:** `fact-ap63203-current-headroom`

  **Value:** 0.35 · **Unit:** `ratio`

  **Conditions:** recommended inductor DC current rating headroom over maximum load

  **Verdict:** PASS - primary-source confirmed · **Provenance:** PRIMARY-SPEC

  **Evidence:** [src-ap6320x-ds41326: Section Inductor row DC current rating at least 35% higher](#src-ap6320x-ds41326)
</EvidenceFact>

<EvidenceFact>
  <EvidenceAnchor id="fact-ap63203-dcr-max" />

  **Fact:** `fact-ap63203-dcr-max`

  **Value:** 0.1 · **Unit:** `ohm`

  **Conditions:** inductor DCR for highest efficiency

  **Verdict:** PASS - primary-source confirmed · **Provenance:** PRIMARY-SPEC

  **Evidence:** [src-ap6320x-ds41326: Section Inductor row DCR less than 100mOhm](#src-ap6320x-ds41326)
</EvidenceFact>

<EvidenceFact>
  <EvidenceAnchor id="fact-ap63203-cap-min" />

  **Fact:** `fact-ap63203-cap-min`

  **Value:** 22 · **Unit:** `uF`

  **Conditions:** general low-ESR ceramic output capacitance envelope

  **Verdict:** PASS - primary-source confirmed · **Provenance:** PRIMARY-SPEC

  **Evidence:** [src-ap6320x-ds41326: Section Output Capacitor row 22uF to 68uF](#src-ap6320x-ds41326)
</EvidenceFact>

<EvidenceFact>
  <EvidenceAnchor id="fact-ap63203-cap-max" />

  **Fact:** `fact-ap63203-cap-max`

  **Value:** 68 · **Unit:** `uF`

  **Conditions:** general low-ESR ceramic output capacitance envelope

  **Verdict:** PASS - primary-source confirmed · **Provenance:** PRIMARY-SPEC

  **Evidence:** [src-ap6320x-ds41326: Section Output Capacitor row 22uF to 68uF](#src-ap6320x-ds41326)
</EvidenceFact>

### GUARANTEED\_ELECTRICAL

A parameter the manufacturer guarantees over the stated conditions, usually with minimum, typical and maximum values.

<EvidenceFact>
  <EvidenceAnchor id="fact-ap63203-vout-min" />

  **Fact:** `fact-ap63203-vout-min`

  **Value:** 3.27 · **Unit:** `V`

  **Conditions:** CCM, recommended ambient/input range

  **Verdict:** PASS - primary-source confirmed · **Provenance:** PRIMARY-SPEC

  **Evidence:** [src-ap6320x-ds41326: Electrical Characteristics table row AP63203 VFB minimum](#src-ap6320x-ds41326)
</EvidenceFact>

<EvidenceFact>
  <EvidenceAnchor id="fact-ap63203-vout-max" />

  **Fact:** `fact-ap63203-vout-max`

  **Value:** 3.33 · **Unit:** `V`

  **Conditions:** CCM, recommended ambient/input range

  **Verdict:** PASS - primary-source confirmed · **Provenance:** PRIMARY-SPEC

  **Evidence:** [src-ap6320x-ds41326: Electrical Characteristics table row AP63203 VFB maximum](#src-ap6320x-ds41326)
</EvidenceFact>

<EvidenceFact>
  <EvidenceAnchor id="fact-ap63203-frequency" />

  **Fact:** `fact-ap63203-frequency`

  **Value:** 1.1 · **Unit:** `MHz`

  **Conditions:** AP63203 oscillator typical with +/-6% frequency spread spectrum

  **Verdict:** NEEDS BENCH · **Provenance:** PRIMARY-SPEC

  **Evidence:** [src-ap6320x-ds41326: Electrical Characteristics table rows fSW and FSS](#src-ap6320x-ds41326)
</EvidenceFact>

<EvidenceFact>
  <EvidenceAnchor id="fact-ap63203-min-on-time" />

  **Fact:** `fact-ap63203-min-on-time`

  **Value:** 80 · **Unit:** `ns`

  **Conditions:** minimum on-time typical table value

  **Verdict:** NEEDS BENCH · **Provenance:** PRIMARY-SPEC

  **Evidence:** [src-ap6320x-ds41326: Electrical Characteristics table row tON](#src-ap6320x-ds41326)
</EvidenceFact>

<EvidenceFact>
  <EvidenceAnchor id="fact-ap63203-soft-start" />

  **Fact:** `fact-ap63203-soft-start`

  **Value:** 4 · **Unit:** `ms`

  **Conditions:** built-in soft-start typical

  **Verdict:** NEEDS BENCH · **Provenance:** PRIMARY-SPEC

  **Evidence:** [src-ap6320x-ds41326: Electrical Characteristics table row tSS and Section Enable](#src-ap6320x-ds41326)
</EvidenceFact>

<EvidenceFact>
  <EvidenceAnchor id="fact-ap63203-peak-limit-min" />

  **Fact:** `fact-ap63203-peak-limit-min`

  **Value:** 2.5 · **Unit:** `A`

  **Conditions:** high-side cycle-by-cycle peak current limit minimum

  **Verdict:** PASS - primary-source confirmed · **Provenance:** PRIMARY-SPEC

  **Evidence:** [src-ap6320x-ds41326: Electrical Characteristics table row IPEAK\_LIMIT minimum](#src-ap6320x-ds41326)
</EvidenceFact>

### TRANSIENT

Behaviour during a short event — startup, a switching edge, a fault or a surge.

<EvidenceFact>
  <EvidenceAnchor id="fact-ap63203-vin-transient" />

  **Fact:** `fact-ap63203-vin-transient`

  **Value:** 40 · **Unit:** `V`

  **Conditions:** maximum 400 ms stress pulse; not continuous operation

  **Verdict:** PASS - primary-source confirmed · **Provenance:** PRIMARY-SPEC

  **Evidence:** [src-ap6320x-ds41326: Absolute Maximum Ratings table row VIN 400ms](#src-ap6320x-ds41326)
</EvidenceFact>

<EvidenceFact>
  <EvidenceAnchor id="fact-ap63203-hiccup" />

  **Fact:** `fact-ap63203-hiccup`

  **Value:** 2 ms repeated peak-limit entry then 16 ms off before restart; overview also expresses 512/8192 cycles · **Unit:** `NONE`

  **Conditions:** persistent output overcurrent or short

  **Verdict:** PASS - primary-source confirmed · **Provenance:** PRIMARY-SPEC

  **Evidence:** [src-ap6320x-ds41326: Section Overcurrent Protection and fault timing row](#src-ap6320x-ds41326)
</EvidenceFact>

### THERMAL\_SOA

Thermal and safe-operating-area behaviour: how much the part may dissipate, and under what mounting and ambient conditions.

<EvidenceFact>
  <EvidenceAnchor id="fact-ap63203-thermal" />

  **Fact:** `fact-ap63203-thermal`

  **Value:** thetaJA 89 C/W on stated single-layer 2 oz test board; application text targets TJ \<=125 C although stress table lists 160 C · **Unit:** `NONE`

  **Conditions:** TSOT26; actual PCB differs

  **Verdict:** NEEDS BENCH · **Provenance:** PRIMARY-SPEC

  **Evidence:** [src-ap6320x-ds41326: Thermal Resistance table and Section Power Derating rows TJ](#src-ap6320x-ds41326)
</EvidenceFact>

<EvidenceFact>
  <EvidenceAnchor id="fact-ap63203-layout" />

  **Fact:** `fact-ap63203-layout`

  **Value:** use 2 oz top/bottom copper, GND plane and vias; place VIN capacitors and FB network close; minimize switching loop · **Unit:** `NONE`

  **Conditions:** 2 A-capable PCB implementation

  **Verdict:** PASS - primary-source confirmed · **Provenance:** PRIMARY-SPEC

  **Evidence:** [src-ap6320x-ds41326: Section PCB Layout rows 1-6 and Figure 25](#src-ap6320x-ds41326)
</EvidenceFact>

### PROJECT\_STATE

A value this project recorded about how the part is used here — a chosen operating point, a net assignment, or a derived figure. Not a manufacturer specification.

<EvidenceFact>
  <EvidenceAnchor id="fact-ap63203-manufacturer" />

  **Fact:** `fact-ap63203-manufacturer`

  **Value:** Diodes Incorporated · **Unit:** `NONE`

  **Conditions:** exact AP63203WU-7 orderable identity

  **Verdict:** PASS - primary-source confirmed · **Provenance:** PRIMARY-SPEC

  **Evidence:** [src-ap6320x-ds41326: title block and ordering table row AP63203WU-7](#src-ap6320x-ds41326)
</EvidenceFact>

<EvidenceFact>
  <EvidenceAnchor id="fact-ap63203-en-open" />

  **Fact:** `fact-ap63203-en-open`

  **Value:** leave EN open for automatic startup via internal pull-up · **Unit:** `NONE`

  **Conditions:** default startup without external UVLO divider

  **Verdict:** PASS - primary-source confirmed · **Provenance:** PRIMARY-SPEC

  **Evidence:** [src-ap6320x-ds41326: Pin Descriptions table row EN and Section Enable](#src-ap6320x-ds41326)
</EvidenceFact>

<EvidenceFact>
  <EvidenceAnchor id="fact-ap63203-min-off-time" />

  **Fact:** `fact-ap63203-min-off-time`

  **Value:** not specified; 220 ns BST refresh is not a minimum off-time rating · **Unit:** `NONE`

  **Conditions:** AP63203 switching timing

  **Verdict:** UNSOURCED · **Provenance:** UNVERIFIED

  **Evidence:** [src-ap6320x-ds41326: Electrical Characteristics table and Section Bootstrap Capacitor row 220ns refresh](#src-ap6320x-ds41326)
</EvidenceFact>

<EvidenceFact>
  <EvidenceAnchor id="fact-ap63203-required-inductor-current" />

  **Fact:** `fact-ap63203-required-inductor-current`

  **Value:** 2.7 · **Unit:** `A`

  **Conditions:** full 2 A design envelope using 35% manufacturer headroom

  **Verdict:** PASS - primary-source confirmed · **Provenance:** CALCULATED

  **Evidence:** [`src-ap6320x-ds41326`](#src-ap6320x-ds41326) — CALCULATED: fact-ap63203-load-max times one plus fact-ap63203-current-headroom
</EvidenceFact>

<EvidenceFact>
  <EvidenceAnchor id="fact-ap63203-reference-l" />

  **Fact:** `fact-ap63203-reference-l`

  **Value:** 3.9 · **Unit:** `uH`

  **Conditions:** AP63203 3.3 V reference selection

  **Verdict:** NOT APPLICABLE · **Provenance:** REFERENCE-DESIGN

  **Evidence:** [src-ap6320x-ds41326: Table 2 row AP63203 3.3V](#src-ap6320x-ds41326)
</EvidenceFact>

<EvidenceFact>
  <EvidenceAnchor id="fact-ap63203-reference-cap" />

  **Fact:** `fact-ap63203-reference-cap`

  **Value:** 44 · **Unit:** `uF`

  **Conditions:** AP63203 3.3 V reference selection as 2x22 uF nominal

  **Verdict:** NOT APPLICABLE · **Provenance:** REFERENCE-DESIGN

  **Evidence:** [src-ap6320x-ds41326: Table 2 row AP63203 C2](#src-ap6320x-ds41326)
</EvidenceFact>

<EvidenceFact>
  <EvidenceAnchor id="fact-ap63203-project-nets" />

  **Fact:** `fact-ap63203-project-nets`

  **Value:** U4.1=V3P3; U4.2 EN open; U4.3=V15; U4.4=GND; U4.5=SW\_LOGIC; U4.6=BST · **Unit:** `NONE`

  **Conditions:** current generated Board L source

  **Verdict:** NOT APPLICABLE · **Provenance:** PROJECT-CHOICE

  **Evidence:** [src-ap63203-generator: COMPONENTS table row U4, NETS rows, and NO\_CONNECT row U4.2](#src-ap63203-generator)
</EvidenceFact>

## Calculation dependencies

These values were derived from other recorded facts rather than read from a document. The expression and every input are published so the number can be recomputed instead of trusted. A derived value is never stronger than the weakest fact it depends on.

**Fact:** [`fact-ap63203-required-inductor-current`](#fact-ap63203-required-inductor-current)

**Expression:** `fact_ap63203_load_max * (1 + fact_ap63203_current_headroom)`

**Depends on:**

- [`fact-ap63203-load-max`](#fact-ap63203-load-max)
- [`fact-ap63203-current-headroom`](#fact-ap63203-current-headroom)

## Pin maps

The mapping between schematic pins and PCB pads, or physical terminals for an external part, as recorded. A record may carry more than one map when the same part is documented in more than one context.

### pinmap-ap63203

<EvidenceAnchor id="pinmap-ap63203" />

- **Symbol:** `AP63203WU-7`
- **Footprint:** `TSOT-26_L2.9-W1.6-P0.95-LS2.8-BL`
- **Pins:** 6

<EvidenceDetails label="pin-assignments">
  <EvidenceTable label="pin-assignments">
    | Symbol pin | Name  | Footprint pad | Function                   |
    | ---------- | ----- | ------------- | -------------------------- |
    | `1`        | `FB`  | `1`           | fixed-output sense at V3P3 |
    | `2`        | `EN`  | `2`           | open for automatic startup |
    | `3`        | `VIN` | `3`           | V15 input                  |
    | `4`        | `GND` | `4`           | power ground               |
    | `5`        | `SW`  | `5`           | SW\_LOGIC switching node   |
    | `6`        | `BST` | `6`           | bootstrap node             |
  </EvidenceTable>
</EvidenceDetails>

## Interactions

Behaviour that is not a property of this part alone. Each interaction names the records it spans, the conditions it holds under, and how far it has been confirmed. An interaction that spans several parts appears on every one of their pages, under the same identifier, because it is equally a fact about each.

### int-ap63203-startup

<EvidenceAnchor id="int-ap63203-startup" />

- **Records involved:** `rec-ap63203wu-7` (this record)
- **Conditions:** EN intentionally open, V15 ramp/transient and downstream load defined
- **Verdict:** NEEDS BENCH

**Facts this rests on:**

- [`fact-ap63203-en-open`](#fact-ap63203-en-open)
- [`fact-ap63203-soft-start`](#fact-ap63203-soft-start)
- [`fact-ap63203-vin-recommended-max`](#fact-ap63203-vin-recommended-max)
- [`fact-ap63203-project-nets`](#fact-ap63203-project-nets)

### int-ap63203-power-stage

<EvidenceAnchor id="int-ap63203-power-stage" />

- **Records involved:** `rec-ap63203wu-7` (this record), [`rec-fnr4030s4r7mt`](/docs/components/records/fnr4030s4r7mt/), [`rec-cl21a226maqnnne`](/docs/components/records/cl21a226maqnnne/)
- **Conditions:** full input/load/temperature envelope and PCB layout; nominal capacitance cannot establish guaranteed stability
- **Verdict:** NEEDS BENCH

**Facts this rests on:**

- [`fact-ap63203-required-inductor-current`](#fact-ap63203-required-inductor-current)
- [`fact-ap63203-reference-l`](#fact-ap63203-reference-l)
- [`fact-ap63203-reference-cap`](#fact-ap63203-reference-cap)
- [`fact-fnr-isat-margin`](/docs/components/records/fnr4030s4r7mt/#fact-fnr-isat-margin) on FNR4030S4R7MT
- [`fact-fnr-irated-margin`](/docs/components/records/fnr4030s4r7mt/#fact-fnr-irated-margin) on FNR4030S4R7MT
- [`fact-cl21-effective-capacitance-status`](/docs/components/records/cl21a226maqnnne/#fact-cl21-effective-capacitance-status) on CL21A226MAQNNNE

## Cross-component rules

Rules that span several parts at once and are published in full on the integration page. Each rule's verdict below is that rule's own — it is a statement about the cross-component question, not about this part — and the exact wording of what the rule refuses to conclude is published with the rule itself.

- [`rule-rail-envelope`](/docs/components/integration/#rule-rail-envelope) — rail-envelope — **rule verdict:** UNSOURCED — Whether every part on the input rail stays inside its own recorded limits across a legal power contract, a mis-contract, and a transient clamp event.
- [`rule-usb-pd-nvm-load-switch`](/docs/components/integration/#rule-usb-pd-nvm-load-switch) — usb-pd-nvm-load-switch — **rule verdict:** UNSOURCED — How the power-delivery controller's stored configuration and its enable output drive the load switch, through every state from detached to fault.
- [`rule-ap63203-logic-stage`](/docs/components/integration/#rule-ap63203-logic-stage) — ap63203-logic-stage — **rule verdict:** UNSOURCED — How the logic-rail converter, its inductor and its output capacitor behave together under the real load the microcontroller presents.
- [`rule-evidence-chain`](/docs/components/integration/#rule-evidence-chain) — source-to-bench-chain — **rule verdict:** NEEDS BENCH — How far each claim has travelled from a manufacturer document towards a measurement on real hardware, stage by stage.
- [`rule-c5446803-power-cut`](/docs/components/integration/#rule-c5446803-power-cut) — board-mounted lamp power switching — **rule verdict:** NEEDS BENCH

[All cross-component rules](/docs/components/integration/)

## Sources

Every document cited above, with its identification, when it was retrieved, and what kind of authority it carries. Sources that could not be retrieved are listed too, with their unavailability stated, so a gap in the evidence is visible rather than absent.

### AP63200/AP63201/AP63203/AP63205 3.8V to 32V Input 2A Synchronous Buck

<EvidenceAnchor id="src-ap6320x-ds41326" />

**Source ID:** `src-ap6320x-ds41326` · **Authority:** MANUFACTURER\_PRIMARY

| Field | Recorded value |
| --- | --- |
| Document number | DS41326 |
| Revision | Rev. 3-2 |
| Document date | 2024-11 |
| Retrieved | 2026-08-02 |
| Printed page | 2 of 18 |

**Locator:** Pin Descriptions table; Absolute Maximum and Electrical Characteristics tables; Application Information sections 3-13; Tables 2 and Figures 21/25

**Availability:** AVAILABLE

**Document URL:** [https://www.diodes.com/datasheet/download/AP63200-AP63201-AP63203-AP63205.pdf](https://www.diodes.com/datasheet/download/AP63200-AP63201-AP63203-AP63205.pdf)

### Board L generated schematic specification

<EvidenceAnchor id="src-ap63203-generator" />

**Source ID:** `src-ap63203-generator` · **Authority:** PROJECT\_GENERATOR

| Field | Recorded value |
| --- | --- |
| Document number | scripts/schgen/board\_l\_spec.py |
| Revision | 410bc1a342286dd6c205d6dcec0f248b8a963987 |
| Document date | 2026-08-02 |
| Retrieved | 2026-08-02 |
| Printed page | source file |

**Locator:** COMPONENTS table row U4, NETS rows V15, V3P3, SW\_LOGIC, BST, GND, and NO\_CONNECT row U4.2

**Availability:** AVAILABLE

**Document URL:** [https://raw.githubusercontent.com/Takazudo/zudo-led-lamp/410bc1a342286dd6c205d6dcec0f248b8a963987/scripts/schgen/board\_l\_spec.py](https://raw.githubusercontent.com/Takazudo/zudo-led-lamp/410bc1a342286dd6c205d6dcec0f248b8a963987/scripts/schgen/board_l_spec.py)

## Legend

What the recorded terms on this page mean, in ordinary words. The exact terms above are the ones that count; these descriptions explain them and never replace them.

### Verdict

| Recorded term | What it means |
| --- | --- |
| `NEEDS BENCH` | Cannot be settled from documents. It needs measurement on real hardware before it can be relied on. |
| `NOT APPLICABLE` | The parameter does not apply to this part as it is used here. |
| `PASS - primary-source confirmed` | Confirmed against the manufacturer's own document for this exact part. |
| `UNSOURCED` | No accepted source backs this value yet. Treat it as a claim, not a fact. |

### Provenance

| Recorded term | What it means |
| --- | --- |
| `CALCULATED` | Derived arithmetically from other facts listed here. The expression and every input are shown, so the number can be recomputed rather than trusted. |
| `PRIMARY-SPEC` | Taken from the manufacturer's own specification document. |
| `PROJECT-CHOICE` | A decision made by this project. No vendor asserts it. |
| `REFERENCE-DESIGN` | Taken from a vendor reference design or application note rather than the device specification. |
| `UNVERIFIED` | Recorded, but not yet backed by an accepted source. |

### Fact class

| Recorded term | What it means |
| --- | --- |
| `ABSOLUTE_MAXIMUM` | A never-exceed limit. Reaching it may damage the part; it is not an operating target and there is no margin implied by it. |
| `GUARANTEED_ELECTRICAL` | A parameter the manufacturer guarantees over the stated conditions, usually with minimum, typical and maximum values. |
| `PROJECT_STATE` | A value this project recorded about how the part is used here — a chosen operating point, a net assignment, or a derived figure. Not a manufacturer specification. |
| `RECOMMENDED_OPERATION` | The range the manufacturer intends the part to be used in. Always narrower than the absolute maximum. |
| `THERMAL_SOA` | Thermal and safe-operating-area behaviour: how much the part may dissipate, and under what mounting and ambient conditions. |
| `TRANSIENT` | Behaviour during a short event — startup, a switching edge, a fault or a surge. |

### Coverage status

| Recorded term | What it means |
| --- | --- |
| `COVERED` | Every question this domain asks is answered by the facts listed against it. |
| `OPEN` | Unresolved. Open means the question has not been answered, not that the part is unsafe — the reason states what is missing. |

### Source availability

| Recorded term | What it means |
| --- | --- |
| `AVAILABLE` | The document was retrieved and is on record. |

### Source authority

| Recorded term | What it means |
| --- | --- |
| `MANUFACTURER_PRIMARY` | The manufacturer's own document for this exact part. |
| `PROJECT_GENERATOR` | A document this project generated, such as a schematic or netlist export. |

### Identity state

| Recorded term | What it means |
| --- | --- |
| `UNRESOLVED`  | The exact orderable part is not yet confirmed. Substituting a same-name part from another vendor is not permitted on that basis. |

### Source state

| Recorded term | What it means |
| --- | --- |
| `SOURCE UNAVAILABLE` | No document backing this line could be retrieved. |

### Unit

| Recorded term | What it means |
| --- | --- |
| `NONE` | The value is not a physical quantity, so it carries no unit. Recorded as \`NONE\`. |

## Raw agent resource

This page is generated from a stored evidence bundle and does not restate it. The bundle is the source of truth: where the two ever disagree, the bundle is right and this page is stale.

[Open the owning bundle](/docs/claude-skills/component-ap63203wu-7/) `component-ap63203wu-7`
