Takazudo/zudo-led-lamp/doc/src/content/docs/components/records/bsmd1206-075-30v/index.mdx

---
# GENERATED by doc/component-docs — do not edit; run `pnpm generate:components`
title: "BSMD1206-075-30V"
description: "750 mA PPTC fuse — BHFUSE — C976305 — board-l F1 — rec-bsmd1206-075-30v"
sidebar_position: 19
---

<EvidenceAnchor id="rec-bsmd1206-075-30v" />

Everything below is projected from this project's stored component evidence. Values keep the exact wording, conditions, units and verdicts they were recorded with — nothing here is re-typed, corrected, or combined into an overall judgement about the part.

This record in the catalog: [BSMD1206-075-30V](/docs/components/catalog/#rec-bsmd1206-075-30v)

## Identity

| Field | Recorded value |
| --- | --- |
| Record ID | `rec-bsmd1206-075-30v` |
| Record kind | standalone |
| Manufacturer part number | `BSMD1206-075-30V` |
| Manufacturer | BHFUSE |
| Function | 750 mA PPTC fuse |
| LCSC ID | `C976305` |
| Package | `F1206` |
| Inventory line | `line-c976305` |
| Also known as | `Board L input resettable fuse` |
| Owner skill | `component-bhfuse-bsmd1206-075-30v` |

**Fit:** Fitted

**Identity state:** UNRESOLVED

**Source state:** SOURCE UNAVAILABLE

**Coverage:** 1 open of 3 published

## Documents and package

<EvidenceAnchor id="component-references-heading" />

<ComponentReferences descriptor="7b2276657273696f6e223a312c22646f63756d656e74223a7b226c6162656c223a2244617461736865657420504446222c227469746c65223a2242534d4431323036205365726965732053757266616365204d6f756e742050544320446576696365222c22617574686f72697479223a224d414e5546414354555245525f5052494d415259222c22617661696c6162696c697479223a22415641494c41424c45222c2275726c223a2268747470733a2f2f626169686f6e672d6f73732e6f73732d636e2d7368656e7a68656e2e616c6979756e63732e636f6d2f626169686f6e672f313230362532304461746173686565742e706466227d2c22666f6f747072696e74223a7b226e616d65223a224631323036222c22617373657455726c223a222f6173736574732f636f6d706f6e656e742d70726576696577732f666f6f747072696e74732f46313230362e737667227d2c226d6f64656c44657363726970746f72223a22376232323736363537323733363936663665323233613331326332323730363136333662363136373635343936343232336132323436333133323330333632323263323237303631363336623631363736353463363136323635366332323361323234363331333233303336323232633232366436663634363536633535373236633232336132323266363137333733363537343733326636333666366437303666366536353665373432643730373236353736363936353737373332663664366636343635366337333266343633313332333033363566346333333265333232643537333132653337326434383330326533363265373737323663323232633232366636363636373336353734323233613762323237383232336133303263323237393232336133303263323237613232336133303764326332323732366637343631373436393666366532323361376232323738323233613330326332323739323233613330326332323761323233613330376432633232373336333631366336353232336137623232373832323361333132633232373932323361333132633232376132323361333137643764227d" />

**Selected document:** [Datasheet PDF](https://baihong-oss.oss-cn-shenzhen.aliyuncs.com/baihong/1206%20Datasheet.pdf) — BSMD1206 Series Surface Mount PTC Device

**Selected source ID:** `src-bhfuse-1206`

**Authority:** MANUFACTURER\_PRIMARY

**Availability:** AVAILABLE

**Package footprint:** `F1206`

This geometry represents a shared footprint package and may not exactly match the manufacturer part.

## Placements

Every position this exact line occupies in the as-built design. One line may be placed many times and across more than one board.

| Board | Reference designator |
| --- | --- |
| board-l | `F1` |

## Coverage

Coverage is stated one domain at a time and is never rolled up. A domain marked open is a question that has not been answered; it is not a finding that the part is unsuitable. A record with no open domains has not thereby been declared safe.

### hold-trip-voltage-current-time-resistance

<EvidenceAnchor id="cov-bhfuse-electrical" />

**Coverage ID:** `cov-bhfuse-electrical` · **Status:** COVERED

**Reason:** fact-bhfuse-hold-25c through fact-bhfuse-resistance-reset-max

**Facts in this domain:**

- [`fact-bhfuse-hold-25c`](#fact-bhfuse-hold-25c)
- [`fact-bhfuse-trip-25c`](#fact-bhfuse-trip-25c)
- [`fact-bhfuse-voltage-max`](#fact-bhfuse-voltage-max)
- [`fact-bhfuse-fault-current-max`](#fact-bhfuse-fault-current-max)
- [`fact-bhfuse-trip-power-typ`](#fact-bhfuse-trip-power-typ)
- [`fact-bhfuse-time-trip`](#fact-bhfuse-time-trip)
- [`fact-bhfuse-resistance-min`](#fact-bhfuse-resistance-min)
- [`fact-bhfuse-resistance-reset-max`](#fact-bhfuse-resistance-reset-max)

### ambient-derating-cycling-reset-processing-package

<EvidenceAnchor id="cov-bhfuse-thermal" />

**Coverage ID:** `cov-bhfuse-thermal` · **Status:** COVERED

**Reason:** fact-bhfuse-hold-85c through fact-bhfuse-package

**Facts in this domain:**

- [`fact-bhfuse-hold-85c`](#fact-bhfuse-hold-85c)
- [`fact-bhfuse-temperature`](#fact-bhfuse-temperature)
- [`fact-bhfuse-surface-temperature`](#fact-bhfuse-surface-temperature)
- [`fact-bhfuse-reset-definition`](#fact-bhfuse-reset-definition)
- [`fact-bhfuse-cycling`](#fact-bhfuse-cycling)
- [`fact-bhfuse-process-warning`](#fact-bhfuse-process-warning)
- [`fact-bhfuse-package`](#fact-bhfuse-package)

### fault-current-ambient-and-cycling

<EvidenceAnchor id="cov-bhfuse-fault" />

**Coverage ID:** `cov-bhfuse-fault` · **Status:** OPEN

**Reason:** The generator does not bound upstream fault current/energy, ambient/local heating, trip count, cooling interval, or downstream normal-load envelope.

**Facts in this domain:** none are recorded against it.

**Blocked by:** no blocking fact is recorded. What is missing has not been reduced to a specific recorded fact, so the reason above is the whole of what is known.

## Facts

Each fact keeps its value, its unit, the conditions it holds under, where it came from and how far it has been confirmed as separate fields, because they are separate claims. A value without its conditions is not the same fact, and a verdict is about the evidence for the value, not about the part.

### ABSOLUTE\_MAXIMUM

A never-exceed limit. Reaching it may damage the part; it is not an operating target and there is no margin implied by it.

<EvidenceFact>
  <EvidenceAnchor id="fact-bhfuse-voltage-max" />

  **Fact:** `fact-bhfuse-voltage-max`

  **Value:** 30 · **Unit:** `Vdc`

  **Conditions:** maximum voltage at rated fault current; exceeding may arc or flame

  **Verdict:** PASS - primary-source confirmed · **Provenance:** PRIMARY-SPEC

  **Evidence:** [src-bhfuse-1206: Electrical Characteristics table row BSMD1206-075-30V Vmax and Warning row 3](#src-bhfuse-1206)
</EvidenceFact>

<EvidenceFact>
  <EvidenceAnchor id="fact-bhfuse-fault-current-max" />

  **Fact:** `fact-bhfuse-fault-current-max`

  **Value:** 40 · **Unit:** `A`

  **Conditions:** maximum fault current at 30 V maximum

  **Verdict:** PASS - primary-source confirmed · **Provenance:** PRIMARY-SPEC

  **Evidence:** [src-bhfuse-1206: Electrical Characteristics table row BSMD1206-075-30V Imax and Vocabulary row Imax](#src-bhfuse-1206)
</EvidenceFact>

### RECOMMENDED\_OPERATION

The range the manufacturer intends the part to be used in. Always narrower than the absolute maximum.

<EvidenceFact>
  <EvidenceAnchor id="fact-bhfuse-temperature" />

  **Fact:** `fact-bhfuse-temperature`

  **Value:** -40 to +85 C ambient · **Unit:** `NONE`

  **Conditions:** operating environment

  **Verdict:** PASS - primary-source confirmed · **Provenance:** PRIMARY-SPEC

  **Evidence:** [src-bhfuse-1206: Environmental Specifications table row Ambient operating conditions](#src-bhfuse-1206)
</EvidenceFact>

<EvidenceFact>
  <EvidenceAnchor id="fact-bhfuse-reset-definition" />

  **Fact:** `fact-bhfuse-reset-definition`

  **Value:** reset is thermal cooling; R1max is measured one hour after trip/reflow, not instant restoration · **Unit:** `NONE`

  **Conditions:** after fault removal

  **Verdict:** PASS - primary-source confirmed · **Provenance:** PRIMARY-SPEC

  **Evidence:** [src-bhfuse-1206: Vocabulary row R1max and Warning row 1](#src-bhfuse-1206)
</EvidenceFact>

### GUARANTEED\_ELECTRICAL

A parameter the manufacturer guarantees over the stated conditions, usually with minimum, typical and maximum values.

<EvidenceFact>
  <EvidenceAnchor id="fact-bhfuse-hold-25c" />

  **Fact:** `fact-bhfuse-hold-25c`

  **Value:** 0.75 · **Unit:** `A`

  **Conditions:** maximum no-trip current in 25 C still air; conventional one-hour hold after one reflow, not long-term charge/discharge rating

  **Verdict:** PASS - primary-source confirmed · **Provenance:** PRIMARY-SPEC

  **Evidence:** [src-bhfuse-1206: Electrical Characteristics table row BSMD1206-075-30V Ihold and Warning row 4](#src-bhfuse-1206)
</EvidenceFact>

<EvidenceFact>
  <EvidenceAnchor id="fact-bhfuse-trip-25c" />

  **Fact:** `fact-bhfuse-trip-25c`

  **Value:** 1.5 · **Unit:** `A`

  **Conditions:** minimum trip current in 25 C still air

  **Verdict:** PASS - primary-source confirmed · **Provenance:** PRIMARY-SPEC

  **Evidence:** [src-bhfuse-1206: Electrical Characteristics table row BSMD1206-075-30V Itrip and Vocabulary row Itrip](#src-bhfuse-1206)
</EvidenceFact>

<EvidenceFact>
  <EvidenceAnchor id="fact-bhfuse-resistance-min" />

  **Fact:** `fact-bhfuse-resistance-min`

  **Value:** 0.09 · **Unit:** `ohm`

  **Conditions:** minimum initial unsoldered resistance at 25 C

  **Verdict:** PASS - primary-source confirmed · **Provenance:** PRIMARY-SPEC

  **Evidence:** [src-bhfuse-1206: Electrical Characteristics table row BSMD1206-075-30V Rmin and Vocabulary row Rmin](#src-bhfuse-1206)
</EvidenceFact>

<EvidenceFact>
  <EvidenceAnchor id="fact-bhfuse-resistance-reset-max" />

  **Fact:** `fact-bhfuse-resistance-reset-max`

  **Value:** 0.5 · **Unit:** `ohm`

  **Conditions:** maximum resistance at 25 C one hour after trip or 260 C/20 s reflow

  **Verdict:** PASS - primary-source confirmed · **Provenance:** PRIMARY-SPEC

  **Evidence:** [src-bhfuse-1206: Electrical Characteristics table row BSMD1206-075-30V R1max and Vocabulary row R1max](#src-bhfuse-1206)
</EvidenceFact>

### TYPICAL\_CURVE

A representative figure read from a characteristic curve. Typical values are not guaranteed and vary part to part.

<EvidenceFact>
  <EvidenceAnchor id="fact-bhfuse-trip-power-typ" />

  **Fact:** `fact-bhfuse-trip-power-typ`

  **Value:** 0.8 · **Unit:** `W`

  **Conditions:** typical tripped-state dissipation at 25 C still air

  **Verdict:** NEEDS BENCH · **Provenance:** PRIMARY-SPEC

  **Evidence:** [src-bhfuse-1206: Electrical Characteristics table row BSMD1206-075-30V Pd typ](#src-bhfuse-1206)
</EvidenceFact>

### TRANSIENT

Behaviour during a short event — startup, a switching edge, a fault or a surge.

<EvidenceFact>
  <EvidenceAnchor id="fact-bhfuse-time-trip" />

  **Fact:** `fact-bhfuse-time-trip`

  **Value:** 0.2 · **Unit:** `s`

  **Conditions:** time to trip at 8 A, 25 C

  **Verdict:** PASS - primary-source confirmed · **Provenance:** PRIMARY-SPEC

  **Evidence:** [src-bhfuse-1206: Electrical Characteristics table row BSMD1206-075-30V Time to trip](#src-bhfuse-1206)
</EvidenceFact>

### THERMAL\_SOA

Thermal and safe-operating-area behaviour: how much the part may dissipate, and under what mounting and ambient conditions.

<EvidenceFact>
  <EvidenceAnchor id="fact-bhfuse-hold-85c" />

  **Fact:** `fact-bhfuse-hold-85c`

  **Value:** 0.41 · **Unit:** `A`

  **Conditions:** 85 C ambient conventional one-hour hold after one reflow

  **Verdict:** PASS - primary-source confirmed · **Provenance:** PRIMARY-SPEC

  **Evidence:** [src-bhfuse-1206: Thermal Derating Chart table row BSMD1206-075 column 85C and Warning row 4](#src-bhfuse-1206)
</EvidenceFact>

<EvidenceFact>
  <EvidenceAnchor id="fact-bhfuse-surface-temperature" />

  **Fact:** `fact-bhfuse-surface-temperature`

  **Value:** 125 · **Unit:** `C`

  **Conditions:** maximum device surface temperature in tripped state

  **Verdict:** PASS - primary-source confirmed · **Provenance:** PRIMARY-SPEC

  **Evidence:** [src-bhfuse-1206: Environmental Specifications table row maximum surface temperature](#src-bhfuse-1206)
</EvidenceFact>

<EvidenceFact>
  <EvidenceAnchor id="fact-bhfuse-cycling" />

  **Fact:** `fact-bhfuse-cycling`

  **Value:** multiple trips reduce hold current; thermal shock typical resistance change can reach +/-33% · **Unit:** `NONE`

  **Conditions:** repeated protection and environmental cycling

  **Verdict:** NEEDS BENCH · **Provenance:** PRIMARY-SPEC

  **Evidence:** [src-bhfuse-1206: Warning row 1 and Environmental Specifications table row Thermal shock](#src-bhfuse-1206)
</EvidenceFact>

<EvidenceFact>
  <EvidenceAnchor id="fact-bhfuse-process-warning" />

  **Fact:** `fact-bhfuse-process-warning`

  **Value:** extra heat processes, hand rework, adhesives, solvents, and nearby heat can degrade parameters; application verification required · **Unit:** `NONE`

  **Conditions:** assembled product history

  **Verdict:** NEEDS BENCH · **Provenance:** PRIMARY-SPEC

  **Evidence:** [src-bhfuse-1206: Warning rows 2 and 5-8](#src-bhfuse-1206)
</EvidenceFact>

### PROJECT\_STATE

A value this project recorded about how the part is used here — a chosen operating point, a net assignment, or a derived figure. Not a manufacturer specification.

<EvidenceFact>
  <EvidenceAnchor id="fact-bhfuse-manufacturer" />

  **Fact:** `fact-bhfuse-manufacturer`

  **Value:** BHFUSE · **Unit:** `NONE`

  **Conditions:** exact BSMD1206-075-30V orderable identity

  **Verdict:** PASS - primary-source confirmed · **Provenance:** PRIMARY-SPEC

  **Evidence:** [src-bhfuse-1206: title block and Electrical Characteristics table row BSMD1206-075-30V](#src-bhfuse-1206)
</EvidenceFact>

<EvidenceFact>
  <EvidenceAnchor id="fact-bhfuse-package" />

  **Fact:** `fact-bhfuse-package`

  **Value:** 1206/3216, nonpolar, marking G for 075 variants · **Unit:** `NONE`

  **Conditions:** surface-mount package

  **Verdict:** PASS - primary-source confirmed · **Provenance:** PRIMARY-SPEC

  **Evidence:** [src-bhfuse-1206: Physical Dimensions table row BSMD1206-075-30V and Figure recommended pad layout](#src-bhfuse-1206)
</EvidenceFact>

<EvidenceFact>
  <EvidenceAnchor id="fact-bhfuse-project-voltage" />

  **Fact:** `fact-bhfuse-project-voltage`

  **Value:** 15 · **Unit:** `V`

  **Conditions:** nominal V15 net label only; upstream transient not bounded

  **Verdict:** NOT APPLICABLE · **Provenance:** PROJECT-CHOICE

  **Evidence:** [src-bhfuse-generator: NETS row V15 and COMPONENTS table row F1](#src-bhfuse-generator)
</EvidenceFact>

<EvidenceFact>
  <EvidenceAnchor id="fact-bhfuse-project-nets" />

  **Fact:** `fact-bhfuse-project-nets`

  **Value:** F1.1=VBUS\_L; F1.2=V15\_FUSED · **Unit:** `NONE`

  **Conditions:** current generated Board L source

  **Verdict:** NOT APPLICABLE · **Provenance:** PROJECT-CHOICE

  **Evidence:** [src-bhfuse-generator: COMPONENTS table row F1 and NETS rows VBUS\_L and V15](#src-bhfuse-generator)
</EvidenceFact>

<EvidenceFact>
  <EvidenceAnchor id="fact-bhfuse-voltage-margin" />

  **Fact:** `fact-bhfuse-voltage-margin`

  **Value:** 15 · **Unit:** `V`

  **Conditions:** 30 V maximum minus nominal V15; upstream surge and fault source impedance unresolved

  **Verdict:** NEEDS BENCH · **Provenance:** CALCULATED

  **Evidence:** [`src-bhfuse-1206`](#src-bhfuse-1206) — CALCULATED: fact-bhfuse-voltage-max minus fact-bhfuse-project-voltage
</EvidenceFact>

## Calculation dependencies

These values were derived from other recorded facts rather than read from a document. The expression and every input are published so the number can be recomputed instead of trusted. A derived value is never stronger than the weakest fact it depends on.

**Fact:** [`fact-bhfuse-voltage-margin`](#fact-bhfuse-voltage-margin)

**Expression:** `fact_bhfuse_voltage_max - fact_bhfuse_project_voltage`

**Depends on:**

- [`fact-bhfuse-voltage-max`](#fact-bhfuse-voltage-max)
- [`fact-bhfuse-project-voltage`](#fact-bhfuse-project-voltage)

## Pin maps

The mapping between schematic pins and PCB pads, or physical terminals for an external part, as recorded. A record may carry more than one map when the same part is documented in more than one context.

### pinmap-bhfuse-075

<EvidenceAnchor id="pinmap-bhfuse-075" />

- **Symbol:** `BSMD1206-075-30V`
- **Footprint:** `F1206`
- **Pins:** 2

<EvidenceDetails label="pin-assignments">
  <EvidenceTable label="pin-assignments">
    | Symbol pin | Name        | Footprint pad | Function          |
    | ---------- | ----------- | ------------- | ----------------- |
    | `1`        | `VBUS_L`    | `1`           | upstream input    |
    | `2`        | `V15_FUSED` | `2`           | fused switch feed |
  </EvidenceTable>
</EvidenceDetails>

## Interactions

Behaviour that is not a property of this part alone. Each interaction names the records it spans, the conditions it holds under, and how far it has been confirmed. An interaction that spans several parts appears on every one of their pages, under the same identifier, because it is equally a fact about each.

### int-bhfuse-input-protection

<EvidenceAnchor id="int-bhfuse-input-protection" />

- **Records involved:** `rec-bsmd1206-075-30v` (this record)
- **Conditions:** actual source fault current/voltage, ambient/local heat, normal load, trip history, and cooling interval
- **Verdict:** NEEDS BENCH

**Facts this rests on:**

- [`fact-bhfuse-hold-25c`](#fact-bhfuse-hold-25c)
- [`fact-bhfuse-trip-25c`](#fact-bhfuse-trip-25c)
- [`fact-bhfuse-time-trip`](#fact-bhfuse-time-trip)
- [`fact-bhfuse-hold-85c`](#fact-bhfuse-hold-85c)
- [`fact-bhfuse-cycling`](#fact-bhfuse-cycling)
- [`fact-bhfuse-project-nets`](#fact-bhfuse-project-nets)
- [`fact-bhfuse-voltage-margin`](#fact-bhfuse-voltage-margin)

## Cross-component rules

Rules that span several parts at once and are published in full on the integration page. Each rule's verdict below is that rule's own — it is a statement about the cross-component question, not about this part — and the exact wording of what the rule refuses to conclude is published with the rule itself.

- [`rule-rail-envelope`](/docs/components/integration/#rule-rail-envelope) — rail-envelope — **rule verdict:** UNSOURCED — Whether every part on the input rail stays inside its own recorded limits across a legal power contract, a mis-contract, and a transient clamp event.
- [`rule-c5446803-power-cut`](/docs/components/integration/#rule-c5446803-power-cut) — board-mounted lamp power switching — **rule verdict:** NEEDS BENCH

[All cross-component rules](/docs/components/integration/)

## Sources

Every document cited above, with its identification, when it was retrieved, and what kind of authority it carries. Sources that could not be retrieved are listed too, with their unavailability stated, so a gap in the evidence is visible rather than absent.

### BSMD1206 Series Surface Mount PTC Device

<EvidenceAnchor id="src-bhfuse-1206" />

**Source ID:** `src-bhfuse-1206` · **Authority:** MANUFACTURER\_PRIMARY

| Field | Recorded value  |
| --- | --- |
| Document number | BSMD1206 Series |
| Revision | Revision 2025 |
| Document date | 2025 |
| Retrieved | 2026-08-02 |
| Printed page | 2/10 |

**Locator:** Electrical Characteristics table row BSMD1206-075-30V; Vocabulary rows; Thermal Derating table row BSMD1206-075; Warning rows 1-6

**Availability:** AVAILABLE

**Document URL:** [https://baihong-oss.oss-cn-shenzhen.aliyuncs.com/baihong/1206%20Datasheet.pdf](https://baihong-oss.oss-cn-shenzhen.aliyuncs.com/baihong/1206%20Datasheet.pdf)

### Board L generated schematic specification

<EvidenceAnchor id="src-bhfuse-generator" />

**Source ID:** `src-bhfuse-generator` · **Authority:** PROJECT\_GENERATOR

| Field | Recorded value |
| --- | --- |
| Document number | scripts/schgen/board\_l\_spec.py |
| Revision | a29a046fc2bc7291704b297cf23a9be5bc000115 |
| Document date | 2026-09-05 |
| Retrieved | 2026-09-05 |
| Printed page | source file |

**Locator:** COMPONENTS table row F1; NETS rows VBUS\_L and V15\_FUSED

**Availability:** AVAILABLE

**Document URL:** [https://raw.githubusercontent.com/Takazudo/zudo-led-lamp/a29a046fc2bc7291704b297cf23a9be5bc000115/scripts/schgen/board\_l\_spec.py](https://raw.githubusercontent.com/Takazudo/zudo-led-lamp/a29a046fc2bc7291704b297cf23a9be5bc000115/scripts/schgen/board_l_spec.py)

## Legend

What the recorded terms on this page mean, in ordinary words. The exact terms above are the ones that count; these descriptions explain them and never replace them.

### Verdict

| Recorded term | What it means |
| --- | --- |
| `NEEDS BENCH` | Cannot be settled from documents. It needs measurement on real hardware before it can be relied on. |
| `NOT APPLICABLE` | The parameter does not apply to this part as it is used here. |
| `PASS - primary-source confirmed` | Confirmed against the manufacturer's own document for this exact part. |

### Provenance

| Recorded term | What it means |
| --- | --- |
| `CALCULATED` | Derived arithmetically from other facts listed here. The expression and every input are shown, so the number can be recomputed rather than trusted. |
| `PRIMARY-SPEC` | Taken from the manufacturer's own specification document. |
| `PROJECT-CHOICE` | A decision made by this project. No vendor asserts it. |

### Fact class

| Recorded term | What it means |
| --- | --- |
| `ABSOLUTE_MAXIMUM` | A never-exceed limit. Reaching it may damage the part; it is not an operating target and there is no margin implied by it. |
| `GUARANTEED_ELECTRICAL` | A parameter the manufacturer guarantees over the stated conditions, usually with minimum, typical and maximum values. |
| `PROJECT_STATE` | A value this project recorded about how the part is used here — a chosen operating point, a net assignment, or a derived figure. Not a manufacturer specification. |
| `RECOMMENDED_OPERATION` | The range the manufacturer intends the part to be used in. Always narrower than the absolute maximum. |
| `THERMAL_SOA` | Thermal and safe-operating-area behaviour: how much the part may dissipate, and under what mounting and ambient conditions. |
| `TRANSIENT` | Behaviour during a short event — startup, a switching edge, a fault or a surge. |
| `TYPICAL_CURVE` | A representative figure read from a characteristic curve. Typical values are not guaranteed and vary part to part. |

### Coverage status

| Recorded term | What it means |
| --- | --- |
| `COVERED` | Every question this domain asks is answered by the facts listed against it. |
| `OPEN` | Unresolved. Open means the question has not been answered, not that the part is unsafe — the reason states what is missing. |

### Source availability

| Recorded term | What it means |
| --- | --- |
| `AVAILABLE` | The document was retrieved and is on record. |

### Source authority

| Recorded term | What it means |
| --- | --- |
| `MANUFACTURER_PRIMARY` | The manufacturer's own document for this exact part. |
| `PROJECT_GENERATOR` | A document this project generated, such as a schematic or netlist export. |

### Identity state

| Recorded term | What it means |
| --- | --- |
| `UNRESOLVED`  | The exact orderable part is not yet confirmed. Substituting a same-name part from another vendor is not permitted on that basis. |

### Source state

| Recorded term | What it means |
| --- | --- |
| `SOURCE UNAVAILABLE` | No document backing this line could be retrieved. |

### Unit

| Recorded term | What it means |
| --- | --- |
| `NONE` | The value is not a physical quantity, so it carries no unit. Recorded as \`NONE\`. |

## Raw agent resource

This page is generated from a stored evidence bundle and does not restate it. The bundle is the source of truth: where the two ever disagree, the bundle is right and this page is stale.

[Open the owning bundle](/docs/claude-skills/component-bhfuse-bsmd1206-075-30v/) `component-bhfuse-bsmd1206-075-30v`
