Takazudo/zudo-led-lamp/doc/src/content/docs/components/records/c13564/index.mdx

---
# GENERATED by doc/component-docs — do not edit; run `pnpm generate:components`
title: "NCP18XH103F03RB"
description: "10 kOhm NTC thermistor — Murata — C13564 — board-l RT1 — rec-c13564"
sidebar_position: 31
---

<EvidenceAnchor id="rec-c13564" />

Everything below is projected from this project's stored component evidence. Values keep the exact wording, conditions, units and verdicts they were recorded with — nothing here is re-typed, corrected, or combined into an overall judgement about the part.

This record in the catalog: [NCP18XH103F03RB](/docs/components/catalog/#rec-c13564)

## Identity

| Field | Recorded value |
| --- | --- |
| Record ID | `rec-c13564` |
| Record kind | standalone |
| Manufacturer part number | `NCP18XH103F03RB` |
| Manufacturer | Murata |
| Function | 10 kOhm NTC thermistor |
| LCSC ID | `C13564` |
| Package | `R0603` |
| Inventory line | `line-c13564` |
| Also known as | `Board L 10 kOhm NTC` |
| Owner skill | `component-murata-ncp18xh103f03rb` |

**Fit:** Fitted

**Identity state:** VERIFIED

**Source state:** AVAILABLE

**Coverage:** 5 open of 6 published

## Documents and package

<EvidenceAnchor id="component-references-heading" />

<ComponentReferences descriptor="7b2276657273696f6e223a312c22646f63756d656e74223a7b226c6162656c223a2253706563696669636174696f6e20504446222c227469746c65223a224d7572617461204e544320546865726d6973746f72732043757272656e742050617274204c697374222c22617574686f72697479223a224d414e5546414354555245525f5052494d415259222c22617661696c6162696c697479223a22415641494c41424c45222c2275726c223a2268747470733a2f2f7777772e6d75726174612e636f6d2f2d2f6d656469612f77656272656e6577616c2f746f6f6c2f6c6962726172792f636f6d6d6f6e2d7064662f7374617469632d6d6f64656c2f636f6d706f6e656e742d6c6973742d6e74632d323530382e617368783f637669643d3230323530393330303131333435303030303030266c613d6a612d6a70227d2c22666f6f747072696e74223a7b226e616d65223a225230363033222c22617373657455726c223a222f6173736574732f636f6d706f6e656e742d70726576696577732f666f6f747072696e74732f52303630332e737667227d2c226d6f64656c44657363726970746f72223a2237623232373636353732373336393666366532323361333132633232373036313633366236313637363534393634323233613232353233303336333033333232326332323730363136333662363136373635346336313632363536633232336132323532333033363330333332323263323236643666363436353663353537323663323233613232326636313733373336353734373332663633366636643730366636653635366537343264373037323635373636393635373737333266366436663634363536633733326635323330333633303333326537373732366332323263323236663636363637333635373432323361376232323738323233613330326332323739323233613330326332323761323233613330376432633232373236663734363137343639366636653232336137623232373832323361333032633232373932323361333032633232376132323361333233373330376432633232373336333631366336353232336137623232373832323361333132633232373932323361333132633232376132323361333137643764227d" />

**Selected document:** [Specification PDF](https://www.murata.com/-/media/webrenewal/tool/library/common-pdf/static-model/component-list-ntc-2508.ashx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\&la=ja-jp) — Murata NTC Thermistors Current Part List

**Selected source ID:** `src-c13564-current`

**Authority:** MANUFACTURER\_PRIMARY

**Availability:** AVAILABLE

**Package footprint:** `R0603`

This geometry represents a shared footprint package and may not exactly match the manufacturer part.

## Placements

Every position this exact line occupies in the as-built design. One line may be placed many times and across more than one board.

| Board | Reference designator |
| --- | --- |
| board-l | `RT1` |

## Coverage

Coverage is stated one domain at a time and is never rolled up. A domain marked open is a question that has not been answered; it is not a finding that the part is unsuitable. A record with no open domains has not thereby been declared safe.

### older-catalog-nominal-context-and-project-divider-topology

<EvidenceAnchor id="cov-c13564-context" />

**Coverage ID:** `cov-c13564-context` · **Status:** OPEN

**Reason:** The 3 genuinely unsourced older-catalog facts (fact-c13564-power, fact-c13564-temperature, fact-c13564-package) retain only lower-authority catalog context and are UNSOURCED, and the generator-derived divider topology fact (fact-c13564-topology) is UNSOURCED pending independent confirmation. The current-primary PASS facts (fact-c13564-resistance, fact-c13564-beta, fact-c13564-max-current, fact-c13564-lifecycle) are confirmed by the current Murata part list and do not belong to this domain.

**Facts in this domain:**

- [`fact-c13564-power`](#fact-c13564-power)
- [`fact-c13564-temperature`](#fact-c13564-temperature)
- [`fact-c13564-package`](#fact-c13564-package)
- [`fact-c13564-topology`](#fact-c13564-topology)

**Blocked by:** these facts must be resolved before the domain can close. Each is listed in full under Facts.

- [`fact-c13564-power`](#fact-c13564-power)
- [`fact-c13564-temperature`](#fact-c13564-temperature)
- [`fact-c13564-package`](#fact-c13564-package)
- [`fact-c13564-topology`](#fact-c13564-topology)

### guaranteed-full-resistance-temperature-table

<EvidenceAnchor id="cov-c13564-rt" />

**Coverage ID:** `cov-c13564-rt` · **Status:** OPEN

**Reason:** fact-c13564-curve-caveat: exact current guaranteed table unavailable

**Facts in this domain:**

- [`fact-c13564-curve-caveat`](#fact-c13564-curve-caveat)

**Blocked by:** these facts must be resolved before the domain can close. Each is listed in full under Facts.

- [`fact-c13564-curve-caveat`](#fact-c13564-curve-caveat)

### installed-dissipation-factor-and-self-heating

<EvidenceAnchor id="cov-c13564-selfheat" />

**Coverage ID:** `cov-c13564-selfheat` · **Status:** OPEN

**Reason:** a nominal Typical Dissipation Constant value now exists in the older catalog mirror (fact-c13564-dissipation) but it is UNSOURCED/unverified nominal context and does not guarantee installed thermal coupling on this PCB

**Facts in this domain:**

- [`fact-c13564-dissipation`](#fact-c13564-dissipation)

**Blocked by:** these facts must be resolved before the domain can close. Each is listed in full under Facts.

- [`fact-c13564-dissipation`](#fact-c13564-dissipation)

### thermal-time-constant-and-placement-response

<EvidenceAnchor id="cov-c13564-time" />

**Coverage ID:** `cov-c13564-time` · **Status:** OPEN

**Reason:** no exact retained time constant or installed placement measurement

**Facts in this domain:** none are recorded against it.

**Blocked by:** no blocking fact is recorded. What is missing has not been reduced to a specific recorded fact, so the reason above is the whole of what is known.

### current-nrnd-lifecycle-confirmation

<EvidenceAnchor id="cov-c13564-life" />

**Coverage ID:** `cov-c13564-life` · **Status:** COVERED

**Reason:** fact-c13564-lifecycle is confirmed by the current manufacturer-primary part list

**Facts in this domain:**

- [`fact-c13564-lifecycle`](#fact-c13564-lifecycle)

### firmware-conversion-and-thresholds

<EvidenceAnchor id="cov-c13564-fw" />

**Coverage ID:** `cov-c13564-fw` · **Status:** OPEN

**Reason:** conversion algorithm, ADC configuration and thresholds are absent

**Facts in this domain:** none are recorded against it.

**Blocked by:** no blocking fact is recorded. What is missing has not been reduced to a specific recorded fact, so the reason above is the whole of what is known.

## Facts

Each fact keeps its value, its unit, the conditions it holds under, where it came from and how far it has been confirmed as separate fields, because they are separate claims. A value without its conditions is not the same fact, and a verdict is about the evidence for the value, not about the part.

### ABSOLUTE\_MAXIMUM

A never-exceed limit. Reaching it may damage the part; it is not an operating target and there is no margin implied by it.

<EvidenceFact>
  <EvidenceAnchor id="fact-c13564-power" />

  **Fact:** `fact-c13564-power`

  **Value:** 100 · **Unit:** `mW`

  **Conditions:** rated electric power in older catalog; installed self-heating remains unknown

  **Verdict:** UNSOURCED · **Provenance:** UNVERIFIED

  **Evidence:** [src-c13564-catalog: section physical page 11 exact row, rated electric power](#src-c13564-catalog)
</EvidenceFact>

<EvidenceFact>
  <EvidenceAnchor id="fact-c13564-temperature" />

  **Fact:** `fact-c13564-temperature`

  **Value:** -40 to 125 C · **Unit:** `NONE`

  **Conditions:** operating range in older catalog

  **Verdict:** UNSOURCED · **Provenance:** UNVERIFIED

  **Evidence:** [src-c13564-catalog: section physical page 11 exact row, operating temperature](#src-c13564-catalog)
</EvidenceFact>

### RECOMMENDED\_OPERATION

The range the manufacturer intends the part to be used in. Always narrower than the absolute maximum.

<EvidenceFact>
  <EvidenceAnchor id="fact-c13564-max-current" />

  **Fact:** `fact-c13564-max-current`

  **Value:** 0.1 · **Unit:** `mA`

  **Conditions:** Murata's own column header for this value is an OPERATING maximum, not a measurement/test-current specification (Japanese header translates to 'Maximum Operating Current, 25C'); corroborated by older catalog src-c13564-catalog physical page index 7, which defines the parallel English term 'Permissive Operating Current' as the current level that keeps the thermistor's own self-heating temperature rise to max. 1C; installed divider current must still be checked against this operating limit across temperature

  **Verdict:** PASS - primary-source confirmed · **Provenance:** PRIMARY-SPEC

  **Evidence:** [src-c13564-current: current part-list table row NCP18XH103F03RB, maximum-current column header (translated from Japanese) reads 'Maximum Operating Current (25C)', identical wording repeated on every page (physical indices 0-4) of the document](#src-c13564-current)
</EvidenceFact>

### GUARANTEED\_ELECTRICAL

A parameter the manufacturer guarantees over the stated conditions, usually with minimum, typical and maximum values.

<EvidenceFact>
  <EvidenceAnchor id="fact-c13564-resistance" />

  **Fact:** `fact-c13564-resistance`

  **Value:** 10 · **Unit:** `kOhm`

  **Conditions:** at 25 C, plus/minus 1%, current part list

  **Verdict:** PASS - primary-source confirmed · **Provenance:** PRIMARY-SPEC

  **Evidence:** [src-c13564-current: current part-list table row NCP18XH103F03RB resistance columns](#src-c13564-current)
</EvidenceFact>

<EvidenceFact>
  <EvidenceAnchor id="fact-c13564-beta" />

  **Fact:** `fact-c13564-beta`

  **Value:** 3380 · **Unit:** `K`

  **Conditions:** B25/50 plus/minus 1%; B25/85 is typical 3434 K; neither is a guaranteed full R-T table

  **Verdict:** PASS - primary-source confirmed · **Provenance:** PRIMARY-SPEC

  **Evidence:** [src-c13564-current: current part-list table row NCP18XH103F03RB B-constant columns](#src-c13564-current)
</EvidenceFact>

### TYPICAL\_CURVE

A representative figure read from a characteristic curve. Typical values are not guaranteed and vary part to part.

<EvidenceFact>
  <EvidenceAnchor id="fact-c13564-curve-caveat" />

  **Fact:** `fact-c13564-curve-caveat`

  **Value:** Exact guaranteed R-T table, installed dissipation factor and thermal time constant are not retained · **Unit:** `NONE`

  **Conditions:** do not substitute beta-only conversion for guaranteed exact-part behavior; dated retrieval attempt 2026-08-02 found no guaranteed exact R-T table and no thermal time constant for this exact part in any reachable primary or mirror source; a nominal Typical Dissipation Constant value was found for the exact part row in the older catalog mirror (see fact-c13564-dissipation) but that is explicitly typical/nominal, not guaranteed, and not the installed value

  **Verdict:** UNSOURCED · **Provenance:** UNVERIFIED

  **Evidence:** [src-c13564-current: current part-list table has no dissipation-constant, time-constant, or full R-T columns; src-c13564-catalog physical page index 7 basic-characteristics section table provides only a generic Typical R/R25-vs-temperature curve for B=3450/3900/4100 families (not this part's B=3380) and defines the terms without giving this part's numeric thermal time constant; Murata SimSurfing tool (murata.com) attempted 2026-08-02 returned only a client-rendered app shell with no server-side data reachable via curl/WebFetch](#src-c13564-current)
</EvidenceFact>

<EvidenceFact>
  <EvidenceAnchor id="fact-c13564-dissipation" />

  **Fact:** `fact-c13564-dissipation`

  **Value:** 1 · **Unit:** `mW/C`

  **Conditions:** typical nominal dissipation constant for the exact NCP18XH103F03RB row in the older catalog; catalog defines the term as the electric power needed to raise the thermistor's own temperature 1C by self-heating; not the installed dissipation factor on this PCB and not a guaranteed spec

  **Verdict:** UNSOURCED · **Provenance:** UNVERIFIED

  **Evidence:** [src-c13564-catalog: section physical page index 11 exact-part ratings table row NCP18XH103F03RB, column 'Typical Dissipation Constant (25C) (mW/C)'](#src-c13564-catalog)
</EvidenceFact>

### PROJECT\_STATE

A value this project recorded about how the part is used here — a chosen operating point, a net assignment, or a derived figure. Not a manufacturer specification.

<EvidenceFact>
  <EvidenceAnchor id="fact-c13564-manufacturer" />

  **Fact:** `fact-c13564-manufacturer`

  **Value:** Murata · **Unit:** `NONE`

  **Conditions:** exact NCP18XH103F03RB current part-list row

  **Verdict:** PASS - primary-source confirmed · **Provenance:** PRIMARY-SPEC

  **Evidence:** [src-c13564-current: current part-list table row NCP18XH103F03RB](#src-c13564-current)
</EvidenceFact>

<EvidenceFact>
  <EvidenceAnchor id="fact-c13564-package" />

  **Fact:** `fact-c13564-package`

  **Value:** 1.6 plus/minus 0.15 by 0.8 plus/minus 0.15 mm chip, nominal 0603 · **Unit:** `NONE`

  **Conditions:** NCP18 dimensions in older catalog

  **Verdict:** UNSOURCED · **Provenance:** UNVERIFIED

  **Evidence:** [src-c13564-catalog: section NCP18 dimensions figure and table](#src-c13564-catalog)
</EvidenceFact>

<EvidenceFact>
  <EvidenceAnchor id="fact-c13564-lifecycle" />

  **Fact:** `fact-c13564-lifecycle`

  **Value:** NRND · **Unit:** `NONE`

  **Conditions:** current Murata part-list status for exact NCP18XH103F03RB

  **Verdict:** PASS - primary-source confirmed · **Provenance:** PRIMARY-SPEC

  **Evidence:** [src-c13564-current: current part-list table row NCP18XH103F03RB status column](#src-c13564-current)
</EvidenceFact>

<EvidenceFact>
  <EvidenceAnchor id="fact-c13564-topology" />

  **Fact:** `fact-c13564-topology`

  **Value:** RT1 from NTC\_SENSE to GND; R26 from V3P3 to NTC\_SENSE; C24 from NTC\_SENSE to GND; U3.11 senses NTC\_SENSE · **Unit:** `NONE`

  **Conditions:** generated Board L netlist

  **Verdict:** UNSOURCED · **Provenance:** PROJECT-CHOICE

  **Evidence:** [src-c13564-generator: section NETS V3P3, NTC\_SENSE and GND](#src-c13564-generator)
</EvidenceFact>

## Pin maps

The mapping between schematic pins and PCB pads, or physical terminals for an external part, as recorded. A record may carry more than one map when the same part is documented in more than one context.

### pinmap-c13564

<EvidenceAnchor id="pinmap-c13564" />

- **Symbol:** `NCP18XH103F03RB`
- **Footprint:** `R0603`
- **Pins:** 2

<EvidenceDetails label="pin-assignments">
  <EvidenceTable label="pin-assignments">
    | Symbol pin | Name         | Footprint pad | Function   |
    | ---------- | ------------ | ------------- | ---------- |
    | `1`        | `terminal-1` | `1`           | NTC\_SENSE |
    | `2`        | `terminal-2` | `2`           | GND        |
  </EvidenceTable>
</EvidenceDetails>

## Interactions

Behaviour that is not a property of this part alone. Each interaction names the records it spans, the conditions it holds under, and how far it has been confirmed. An interaction that spans several parts appears on every one of their pages, under the same identifier, because it is equally a fact about each.

### int-c13564-divider

<EvidenceAnchor id="int-c13564-divider" />

- **Records involved:** `rec-c13564` (this record)
- **Conditions:** ADC conversion needs exact R-T data, pull-up tolerance, V3P3/VREF, acquisition time, RC settling and firmware algorithm
- **Verdict:** NEEDS BENCH

**Facts this rests on:**

- [`fact-c13564-resistance`](#fact-c13564-resistance)
- [`fact-c13564-beta`](#fact-c13564-beta)
- [`fact-c13564-topology`](#fact-c13564-topology)
- [`fact-c13564-curve-caveat`](#fact-c13564-curve-caveat)

### int-c13564-thermal

<EvidenceAnchor id="int-c13564-thermal" />

- **Records involved:** `rec-c13564` (this record)
- **Conditions:** Validate self-heating, PCB/air coupling, thermal lag and thresholds in the installed enclosure
- **Verdict:** NEEDS BENCH

**Facts this rests on:**

- [`fact-c13564-power`](#fact-c13564-power)
- [`fact-c13564-temperature`](#fact-c13564-temperature)
- [`fact-c13564-curve-caveat`](#fact-c13564-curve-caveat)
- [`fact-c13564-dissipation`](#fact-c13564-dissipation)

## Cross-component rules

Rules that span several parts at once and are published in full on the integration page. Each rule's verdict below is that rule's own — it is a statement about the cross-component question, not about this part — and the exact wording of what the rule refuses to conclude is published with the rule itself.

- [`rule-ntc-adc-firmware`](/docs/components/integration/#rule-ntc-adc-firmware) — ntc-adc-firmware — **rule verdict:** UNSOURCED — How the thermistor, its divider, the analog-to-digital input and the firmware that reads them combine into a temperature the design can act on.

[All cross-component rules](/docs/components/integration/)

## Sources

Every document cited above, with its identification, when it was retrieved, and what kind of authority it carries. Sources that could not be retrieved are listed too, with their unavailability stated, so a gap in the evidence is visible rather than absent.

### Murata NTC Thermistors Current Part List

<EvidenceAnchor id="src-c13564-current" />

**Source ID:** `src-c13564-current` · **Authority:** MANUFACTURER\_PRIMARY

| Field | Recorded value |
| --- | --- |
| Document number | component-list-ntc-2508 |
| Revision | 2025-09 current list |
| Document date | 2025-09-30 |
| Retrieved | 2026-08-02 |
| Printed page | 5/5 |

**Locator:** Current part-list table exact row NCP18XH103F03RB

**Availability:** AVAILABLE

**Document URL:** [https://www.murata.com/-/media/webrenewal/tool/library/common-pdf/static-model/component-list-ntc-2508.ashx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\&la=ja-jp](https://www.murata.com/-/media/webrenewal/tool/library/common-pdf/static-model/component-list-ntc-2508.ashx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\&la=ja-jp)

### Murata NTC Thermistors catalog

<EvidenceAnchor id="src-c13564-catalog" />

**Source ID:** `src-c13564-catalog` · **Authority:** MANUFACTURER\_MIRROR

| Field | Recorded value |
| --- | --- |
| Document number | Cat.No.R44E-15 |
| Revision | R44E-15 |
| Document date | 2012-12-17 |
| Retrieved | 2026-08-02 |
| Printed page | 10 |

**Locator:** NCP18 series ratings table, exact NCP18XH103F03RB row

**Availability:** AVAILABLE

**Document URL:** [https://datasheet.lcsc.com/lcsc\_datasheet\_1809202230\_Murata-Electronics-NCP18XH103F03RB\_C13564.pdf](https://datasheet.lcsc.com/lcsc_datasheet_1809202230_Murata-Electronics-NCP18XH103F03RB_C13564.pdf)

### Board L generated schematic specification

<EvidenceAnchor id="src-c13564-generator" />

**Source ID:** `src-c13564-generator` · **Authority:** PROJECT\_GENERATOR

| Field | Recorded value |
| --- | --- |
| Document number | board-l-spec |
| Revision | 410bc1a342286dd6c205d6dcec0f248b8a963987 |
| Document date | 2026-08-01 |
| Retrieved | 2026-08-02 |
| Printed page | source |

**Locator:** Source section PARTS RT1/R26/C24 and NETS V3P3/NTC\_SENSE/GND

**Availability:** AVAILABLE

**Document URL:** [https://raw.githubusercontent.com/Takazudo/zudo-led-lamp/410bc1a342286dd6c205d6dcec0f248b8a963987/scripts/schgen/board\_l\_spec.py](https://raw.githubusercontent.com/Takazudo/zudo-led-lamp/410bc1a342286dd6c205d6dcec0f248b8a963987/scripts/schgen/board_l_spec.py)

## Legend

What the recorded terms on this page mean, in ordinary words. The exact terms above are the ones that count; these descriptions explain them and never replace them.

### Verdict

| Recorded term | What it means |
| --- | --- |
| `PASS - primary-source confirmed` | Confirmed against the manufacturer's own document for this exact part. |
| `UNSOURCED` | No accepted source backs this value yet. Treat it as a claim, not a fact. |

### Provenance

| Recorded term | What it means |
| --- | --- |
| `PRIMARY-SPEC` | Taken from the manufacturer's own specification document. |
| `PROJECT-CHOICE` | A decision made by this project. No vendor asserts it. |
| `UNVERIFIED` | Recorded, but not yet backed by an accepted source. |

### Fact class

| Recorded term | What it means |
| --- | --- |
| `ABSOLUTE_MAXIMUM` | A never-exceed limit. Reaching it may damage the part; it is not an operating target and there is no margin implied by it. |
| `GUARANTEED_ELECTRICAL` | A parameter the manufacturer guarantees over the stated conditions, usually with minimum, typical and maximum values. |
| `PROJECT_STATE` | A value this project recorded about how the part is used here — a chosen operating point, a net assignment, or a derived figure. Not a manufacturer specification. |
| `RECOMMENDED_OPERATION` | The range the manufacturer intends the part to be used in. Always narrower than the absolute maximum. |
| `TYPICAL_CURVE` | A representative figure read from a characteristic curve. Typical values are not guaranteed and vary part to part. |

### Coverage status

| Recorded term | What it means |
| --- | --- |
| `COVERED` | Every question this domain asks is answered by the facts listed against it. |
| `OPEN` | Unresolved. Open means the question has not been answered, not that the part is unsafe — the reason states what is missing. |

### Source availability

| Recorded term | What it means |
| --- | --- |
| `AVAILABLE` | The document was retrieved and is on record. |

### Source authority

| Recorded term | What it means |
| --- | --- |
| `MANUFACTURER_MIRROR`  | A copy of a manufacturer document hosted elsewhere. Usable, but weaker than the manufacturer's own copy. |
| `MANUFACTURER_PRIMARY` | The manufacturer's own document for this exact part. |
| `PROJECT_GENERATOR` | A document this project generated, such as a schematic or netlist export. |

### Identity state

| Recorded term | What it means |
| --- | --- |
| `VERIFIED` | The exact orderable part has been confirmed against a source. |

### Source state

| Recorded term | What it means |
| --- | --- |
| `AVAILABLE` | At least one document backing this line was retrieved. |

### Unit

| Recorded term | What it means |
| --- | --- |
| `NONE` | The value is not a physical quantity, so it carries no unit. Recorded as \`NONE\`. |

## Raw agent resource

This page is generated from a stored evidence bundle and does not restate it. The bundle is the source of truth: where the two ever disagree, the bundle is right and this page is stale.

[Open the owning bundle](/docs/claude-skills/component-murata-ncp18xh103f03rb/) `component-murata-ncp18xh103f03rb`
