Takazudo/zudo-led-lamp/doc/src/content/docs/components/records/c13585/index.mdx

---
# GENERATED by doc/component-docs — do not edit; run `pnpm generate:components`
title: "CL31A106KBHNNNE"
description: "10 uF 50 V MLCC — Samsung Electro-Mechanics — C13585 — board-p C1; board-l C10, C11, C12, C14 — rec-c13585"
sidebar_position: 8
---

<EvidenceAnchor id="rec-c13585" />

Everything below is projected from this project's stored component evidence. Values keep the exact wording, conditions, units and verdicts they were recorded with — nothing here is re-typed, corrected, or combined into an overall judgement about the part.

This record in the catalog: [CL31A106KBHNNNE](/docs/components/catalog/#rec-c13585)

## Identity

| Field | Recorded value |
| --- | --- |
| Record ID | `rec-c13585` |
| Record kind | standalone |
| Manufacturer part number | `CL31A106KBHNNNE` |
| Manufacturer | Samsung Electro-Mechanics |
| Function | 10 uF 50 V MLCC |
| LCSC ID | `C13585` |
| Package | `C1206` |
| Inventory line | `line-c13585` |
| Owner skill | `component-project-passives` |

**Fit:** Fitted

**Identity state:** UNRESOLVED

**Source state:** SOURCE UNAVAILABLE

**Coverage:** 3 open of 5 published

## Documents and package

<EvidenceAnchor id="component-references-heading" />

<ComponentReferences descriptor="7b2276657273696f6e223a312c22646f63756d656e74223a7b226c6162656c223a2253706563696669636174696f6e20504446222c227469746c65223a2253616d73756e6720456c656374726f2d4d656368616e6963732053504543494649434154494f4e20285265666572656e63652053686565742920616e64204d4c43432050726f64756374204d616e75616c20666f7220434c3331413130364b42484e4e4e45222c22617574686f72697479223a224d414e5546414354555245525f5052494d415259222c22617661696c6162696c697479223a22415641494c41424c45222c2275726c223a2268747470733a2f2f70726f647563742e73616d73756e6773656d2e636f6d2f706172742f646f776e6c6f61642e646f3f6d61737465724b65793d434c3331413130364b42484e4e4e26747970653d737065637368656574227d2c22666f6f747072696e74223a7b226e616d65223a224331323036222c22617373657455726c223a222f6173736574732f636f6d706f6e656e742d70726576696577732f666f6f747072696e74732f43313230362e737667227d2c226d6f64656c44657363726970746f72223a22376232323736363537323733363936663665323233613331326332323730363136333662363136373635343936343232336132323433333133323330333632323263323237303631363336623631363736353463363136323635366332323361323234333331333233303336323232633232366436663634363536633535373236633232336132323266363137333733363537343733326636333666366437303666366536353665373432643730373236353736363936353737373332663664366636343635366337333266343333313332333033363566346333333265333232643537333132653336326434383331326533333265373737323663323232633232366636363636373336353734323233613762323237383232336133303263323237393232336133303263323237613232336133303764326332323732366637343631373436393666366532323361376232323738323233613330326332323739323233613330326332323761323233613330376432633232373336333631366336353232336137623232373832323361333132633232373932323361333132633232376132323361333137643764227d" />

**Selected document:** [Specification PDF](https://product.samsungsem.com/part/download.do?masterKey=CL31A106KBHNNN\&type=specsheet) — Samsung Electro-Mechanics SPECIFICATION (Reference Sheet) and MLCC Product Manual for CL31A106KBHNNNE

**Selected source ID:** `src-c13585-page`

**Authority:** MANUFACTURER\_PRIMARY

**Availability:** AVAILABLE

**Package footprint:** `C1206`

This geometry represents a shared footprint package and may not exactly match the manufacturer part.

## Placements

Every position this exact line occupies in the as-built design. One line may be placed many times and across more than one board.

| Board | Reference designator |
| --- | --- |
| board-p | `C1` |
| board-l | `C10` |
| board-l | `C11` |
| board-l | `C12` |
| board-l | `C14` |

## Coverage

Coverage is stated one domain at a time and is never rolled up. A domain marked open is a question that has not been answered; it is not a finding that the part is unsuitable. A record with no open domains has not thereby been declared safe.

### identity-and-rated-capacitance

<EvidenceAnchor id="cov-c13585-identity" />

**Coverage ID:** `cov-c13585-identity` · **Status:** COVERED

**Reason:** fact-c13585-manufacturer; fact-c13585-capacitance; fact-c13585-voltage

**Facts in this domain:**

- [`fact-c13585-manufacturer`](#fact-c13585-manufacturer)
- [`fact-c13585-capacitance`](#fact-c13585-capacitance)
- [`fact-c13585-voltage`](#fact-c13585-voltage)

### dielectric-temperature-and-termination

<EvidenceAnchor id="cov-c13585-temp" />

**Coverage ID:** `cov-c13585-temp` · **Status:** COVERED

**Reason:** fact-c13585-dielectric; fact-c13585-package

**Facts in this domain:**

- [`fact-c13585-dielectric`](#fact-c13585-dielectric)
- [`fact-c13585-package`](#fact-c13585-package)

### effective-capacitance-under-installed-bias

<EvidenceAnchor id="cov-c13585-bias" />

**Coverage ID:** `cov-c13585-bias` · **Status:** OPEN

**Reason:** fact-c13585-curve-caveat: installed voltage/curve point is not retained

**Facts in this domain:**

- [`fact-c13585-curve-caveat`](#fact-c13585-curve-caveat)

**Blocked by:** these facts must be resolved before the domain can close. Each is listed in full under Facts.

- [`fact-c13585-curve-caveat`](#fact-c13585-curve-caveat)

### aging-at-installed-condition

<EvidenceAnchor id="cov-c13585-aging" />

**Coverage ID:** `cov-c13585-aging` · **Status:** OPEN

**Reason:** fact-c13585-curve-caveat: exact aging data/condition is not retained

**Facts in this domain:**

- [`fact-c13585-curve-caveat`](#fact-c13585-curve-caveat)

**Blocked by:** these facts must be resolved before the domain can close. Each is listed in full under Facts.

- [`fact-c13585-curve-caveat`](#fact-c13585-curve-caveat)

### ripple-current-under-installed-layout

<EvidenceAnchor id="cov-c13585-ripple" />

**Coverage ID:** `cov-c13585-ripple` · **Status:** OPEN

**Reason:** fact-c13585-curve-caveat: typical curve is not a guaranteed layout-specific limit

**Facts in this domain:**

- [`fact-c13585-curve-caveat`](#fact-c13585-curve-caveat)

**Blocked by:** these facts must be resolved before the domain can close. Each is listed in full under Facts.

- [`fact-c13585-curve-caveat`](#fact-c13585-curve-caveat)

## Facts

Each fact keeps its value, its unit, the conditions it holds under, where it came from and how far it has been confirmed as separate fields, because they are separate claims. A value without its conditions is not the same fact, and a verdict is about the evidence for the value, not about the part.

### ABSOLUTE\_MAXIMUM

A never-exceed limit. Reaching it may damage the part; it is not an operating target and there is no margin implied by it.

<EvidenceFact>
  <EvidenceAnchor id="fact-c13585-voltage" />

  **Fact:** `fact-c13585-voltage`

  **Value:** 50 · **Unit:** `Vdc`

  **Conditions:** rated voltage

  **Verdict:** PASS - primary-source confirmed · **Provenance:** PRIMARY-SPEC

  **Evidence:** [src-c13585-page: physical page 1, Section A Samsung Part Number, row Rated Voltage](#src-c13585-page)
</EvidenceFact>

### GUARANTEED\_ELECTRICAL

A parameter the manufacturer guarantees over the stated conditions, usually with minimum, typical and maximum values.

<EvidenceFact>
  <EvidenceAnchor id="fact-c13585-capacitance" />

  **Fact:** `fact-c13585-capacitance`

  **Value:** 10 · **Unit:** `uF`

  **Conditions:** nominal capacitance for exact CL31A106KBHNNNE

  **Verdict:** PASS - primary-source confirmed · **Provenance:** PRIMARY-SPEC

  **Evidence:** [src-c13585-page: physical page 1, Section A Samsung Part Number, row Capacitance](#src-c13585-page)
</EvidenceFact>

<EvidenceFact>
  <EvidenceAnchor id="fact-c13585-tolerance" />

  **Fact:** `fact-c13585-tolerance`

  **Value:** 10 · **Unit:** `%`

  **Conditions:** plus/minus tolerance

  **Verdict:** PASS - primary-source confirmed · **Provenance:** PRIMARY-SPEC

  **Evidence:** [src-c13585-page: physical page 1, Section A Samsung Part Number, row Capacitance tolerance](#src-c13585-page)
</EvidenceFact>

<EvidenceFact>
  <EvidenceAnchor id="fact-c13585-dielectric" />

  **Fact:** `fact-c13585-dielectric`

  **Value:** X5R, -55 to +85 C, plus/minus 15% TCC · **Unit:** `NONE`

  **Conditions:** temperature characteristic for exact reference sheet

  **Verdict:** PASS - primary-source confirmed · **Provenance:** PRIMARY-SPEC

  **Evidence:** [src-c13585-page: physical page 2, Section C reliability table, row Temperature Characteristics](#src-c13585-page)
</EvidenceFact>

### TYPICAL\_CURVE

A representative figure read from a characteristic curve. Typical values are not guaranteed and vary part to part.

<EvidenceFact>
  <EvidenceAnchor id="fact-c13585-curve-caveat" />

  **Fact:** `fact-c13585-curve-caveat`

  **Value:** Typical DC-bias, AC-voltage, ripple-current and temperature curves are design reference only · **Unit:** `NONE`

  **Conditions:** reference-sheet product manual; installed DC bias, AC voltage, temperature and layout not supplied

  **Verdict:** NEEDS BENCH · **Provenance:** PRIMARY-SPEC

  **Evidence:** [src-c13585-page: physical pages 13-14, Sections 2-1-3 and 2-5; physical pages 15-16, Sections 2-6 self-heating/ripple and 2-7 DC/AC voltage examples; physical page 32, Section 5-3](#src-c13585-page)
</EvidenceFact>

### PROJECT\_STATE

A value this project recorded about how the part is used here — a chosen operating point, a net assignment, or a derived figure. Not a manufacturer specification.

<EvidenceFact>
  <EvidenceAnchor id="fact-c13585-manufacturer" />

  **Fact:** `fact-c13585-manufacturer`

  **Value:** Samsung Electro-Mechanics · **Unit:** `NONE`

  **Conditions:** exact orderable CL31A106KBHNNNE

  **Verdict:** PASS - primary-source confirmed · **Provenance:** PRIMARY-SPEC

  **Evidence:** [src-c13585-page: physical page 1, title block and Section A Samsung Part Number](#src-c13585-page)
</EvidenceFact>

<EvidenceFact>
  <EvidenceAnchor id="fact-c13585-package" />

  **Fact:** `fact-c13585-package`

  **Value:** 1206/3216, Ni/Cu/Ni/Sn termination · **Unit:** `NONE`

  **Conditions:** part-number codes 31 and N

  **Verdict:** PASS - primary-source confirmed · **Provenance:** PRIMARY-SPEC

  **Evidence:** [src-c13585-catalog: Part Numbering, Size Code and Design Code tables](#src-c13585-catalog)
</EvidenceFact>

## Pin maps

The mapping between schematic pins and PCB pads, or physical terminals for an external part, as recorded. A record may carry more than one map when the same part is documented in more than one context.

### pinmap-c13585

<EvidenceAnchor id="pinmap-c13585" />

- **Symbol:** `CL31A106KBHNNNE`
- **Footprint:** `C1206`
- **Pins:** 2

<EvidenceDetails label="pin-assignments">
  <EvidenceTable label="pin-assignments">
    | Symbol pin | Name         | Footprint pad | Function         |
    | ---------- | ------------ | ------------- | ---------------- |
    | `1`        | `terminal-1` | `1`           | passive terminal |
    | `2`        | `terminal-2` | `2`           | passive terminal |
  </EvidenceTable>
</EvidenceDetails>

## Interactions

Behaviour that is not a property of this part alone. Each interaction names the records it spans, the conditions it holds under, and how far it has been confirmed. An interaction that spans several parts appears on every one of their pages, under the same identifier, because it is equally a fact about each.

### int-c13585-placement

<EvidenceAnchor id="int-c13585-placement" />

- **Records involved:** `rec-c13585` (this record)
- **Conditions:** C1 and Board L C10/C11/C12/C14 placements; effective capacitance is conditional
- **Verdict:** NEEDS BENCH

**Facts this rests on:**

- [`fact-c13585-capacitance`](#fact-c13585-capacitance)
- [`fact-c13585-voltage`](#fact-c13585-voltage)
- [`fact-c13585-curve-caveat`](#fact-c13585-curve-caveat)

## Cross-component rules

Rules that span several parts at once and are published in full on the integration page. Each rule's verdict below is that rule's own — it is a statement about the cross-component question, not about this part — and the exact wording of what the rule refuses to conclude is published with the rule itself.

- [`rule-rail-envelope`](/docs/components/integration/#rule-rail-envelope) — rail-envelope — **rule verdict:** UNSOURCED — Whether every part on the input rail stays inside its own recorded limits across a legal power contract, a mis-contract, and a transient clamp event.

[All cross-component rules](/docs/components/integration/)

## Sources

Every document cited above, with its identification, when it was retrieved, and what kind of authority it carries. Sources that could not be retrieved are listed too, with their unavailability stated, so a gap in the evidence is visible rather than absent.

### Samsung Electro-Mechanics SPECIFICATION (Reference Sheet) and MLCC Product Manual for CL31A106KBHNNNE

<EvidenceAnchor id="src-c13585-page" />

**Source ID:** `src-c13585-page` · **Authority:** MANUFACTURER\_PRIMARY

| Field | Recorded value |
| --- | --- |
| Document number | CL31A106KBHNNNE |
| Revision | Issued 2024-05-09 |
| Document date | 2024-05-09 |
| Retrieved | 2026-08-02 |
| Printed page | 1 (first sheet) |

**Locator:** Physical page 1, Section A Samsung Part Number and Section B Structure & Dimension; physical page 2, Section C reliability table

**Availability:** AVAILABLE

**Document URL:** [https://product.samsungsem.com/part/download.do?masterKey=CL31A106KBHNNN\&type=specsheet](https://product.samsungsem.com/part/download.do?masterKey=CL31A106KBHNNN\&type=specsheet)

### Samsung Electro-Mechanics MLCC catalog

<EvidenceAnchor id="src-c13585-catalog" />

**Source ID:** `src-c13585-catalog` · **Authority:** MANUFACTURER\_PRIMARY

| Field | Recorded value |
| --- | --- |
| Document number | MLCC\_2512 |
| Revision | December 2025  |
| Document date | 2025-12-01 |
| Retrieved | 2026-08-02 |
| Printed page | 06 |

**Locator:** Part Numbering, size/delectric/termination code tables

**Availability:** AVAILABLE

**Document URL:** [https://www.samsungsem.com/resources/file/jp/support/product\_catalog/MLCC\_2512.pdf](https://www.samsungsem.com/resources/file/jp/support/product_catalog/MLCC_2512.pdf)

## Legend

What the recorded terms on this page mean, in ordinary words. The exact terms above are the ones that count; these descriptions explain them and never replace them.

### Verdict

| Recorded term | What it means |
| --- | --- |
| `NEEDS BENCH` | Cannot be settled from documents. It needs measurement on real hardware before it can be relied on. |
| `PASS - primary-source confirmed` | Confirmed against the manufacturer's own document for this exact part. |

### Provenance

| Recorded term  | What it means |
| --- | --- |
| `PRIMARY-SPEC` | Taken from the manufacturer's own specification document. |

### Fact class

| Recorded term | What it means |
| --- | --- |
| `ABSOLUTE_MAXIMUM` | A never-exceed limit. Reaching it may damage the part; it is not an operating target and there is no margin implied by it. |
| `GUARANTEED_ELECTRICAL` | A parameter the manufacturer guarantees over the stated conditions, usually with minimum, typical and maximum values. |
| `PROJECT_STATE` | A value this project recorded about how the part is used here — a chosen operating point, a net assignment, or a derived figure. Not a manufacturer specification. |
| `TYPICAL_CURVE` | A representative figure read from a characteristic curve. Typical values are not guaranteed and vary part to part. |

### Coverage status

| Recorded term | What it means |
| --- | --- |
| `COVERED` | Every question this domain asks is answered by the facts listed against it. |
| `OPEN` | Unresolved. Open means the question has not been answered, not that the part is unsafe — the reason states what is missing. |

### Source availability

| Recorded term | What it means |
| --- | --- |
| `AVAILABLE` | The document was retrieved and is on record. |

### Source authority

| Recorded term | What it means |
| --- | --- |
| `MANUFACTURER_PRIMARY` | The manufacturer's own document for this exact part. |
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
