Takazudo/zudo-led-lamp/doc/public/assets/enclosure/stl/foot-03.stl

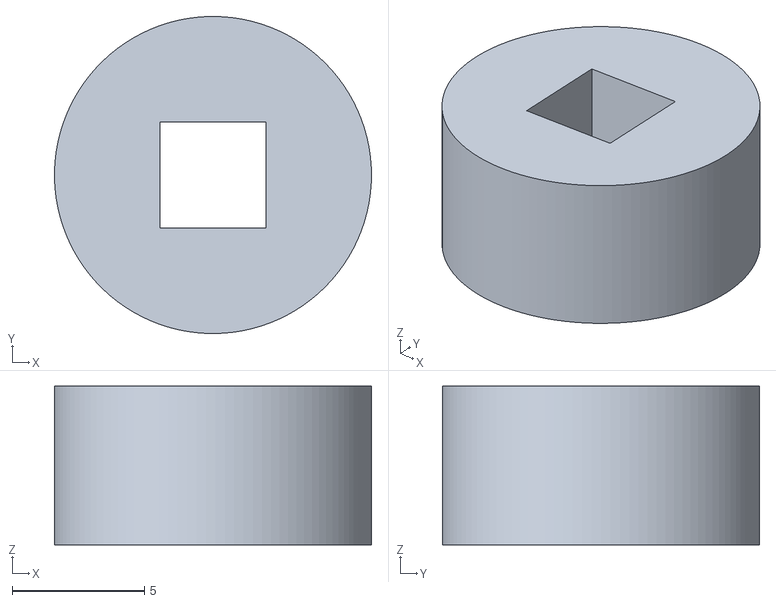
[picture p15: CAD file, 2026-09-08]
doc/public/assets/enclosure/stl/foot-03.stl
12.0 x 12.0 x 6.00
