Takazudo/zudo-led-lamp/doc/public/assets/enclosure/stl/mount-02-17.6mm.stl

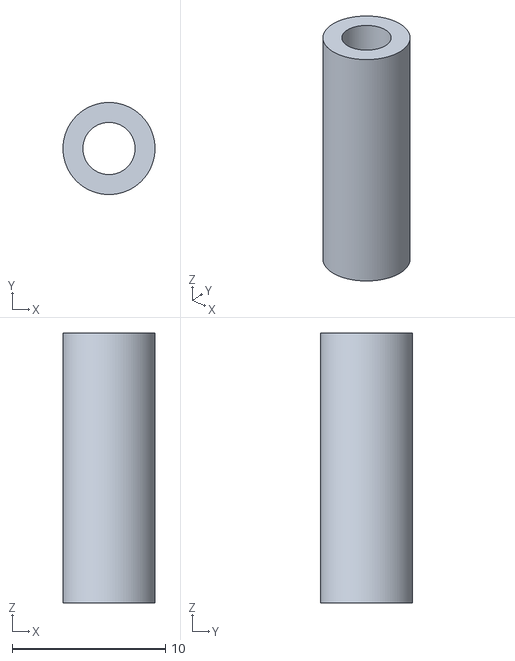
[picture p16: CAD file, 2026-09-08]
doc/public/assets/enclosure/stl/mount-02-17.6mm.stl
6.00 x 6.00 x 17.6
