Takazudo/zudo-led-lamp/doc/public/assets/enclosure/stl/06-band-top.stl

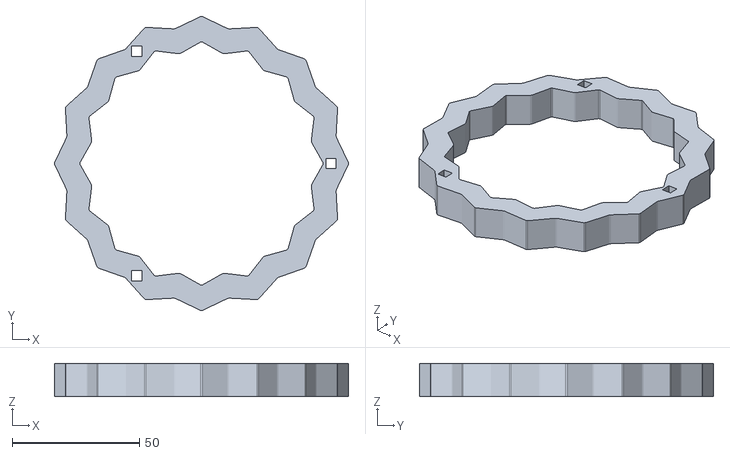
[picture p17: CAD file, 2026-09-08]
doc/public/assets/enclosure/stl/06-band-top.stl
115.7 x 115.7 x 13.0
