Takazudo/zudo-led-lamp/doc/public/assets/enclosure/stl/test-square-post-flat.stl

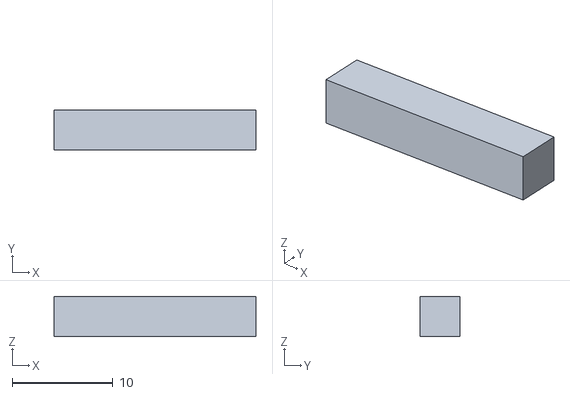
[picture p18: CAD file, 2026-09-08]
doc/public/assets/enclosure/stl/test-square-post-flat.stl
20.0 x 4.00 x 4.00
