Takazudo/zudo-led-lamp/doc/public/assets/enclosure/stl/test-pin-2.4.stl

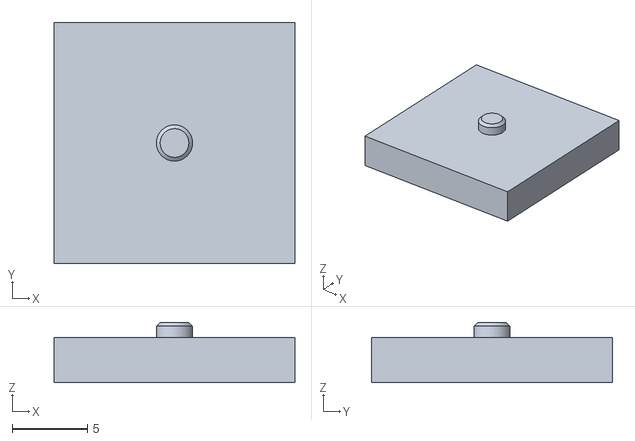
[picture p19: CAD file, 2026-09-08]
doc/public/assets/enclosure/stl/test-pin-2.4.stl
16.0 x 16.0 x 4.00
