Takazudo/zudo-led-lamp/manufacturing/jlcpcb/2026-09-19/board-l/gerber-bottom.png

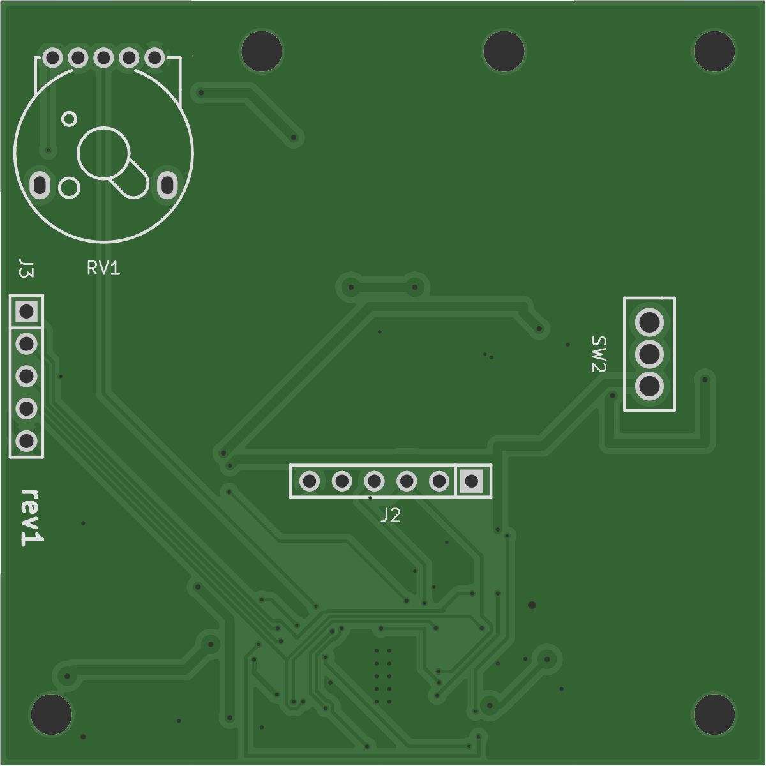
manufacturing/jlcpcb/2026-09-19/board-l/gerber-bottom.png
