Takazudo/zudo-led-lamp/manufacturing/jlcpcb/2026-09-19/board-p/gerber-bottom.png

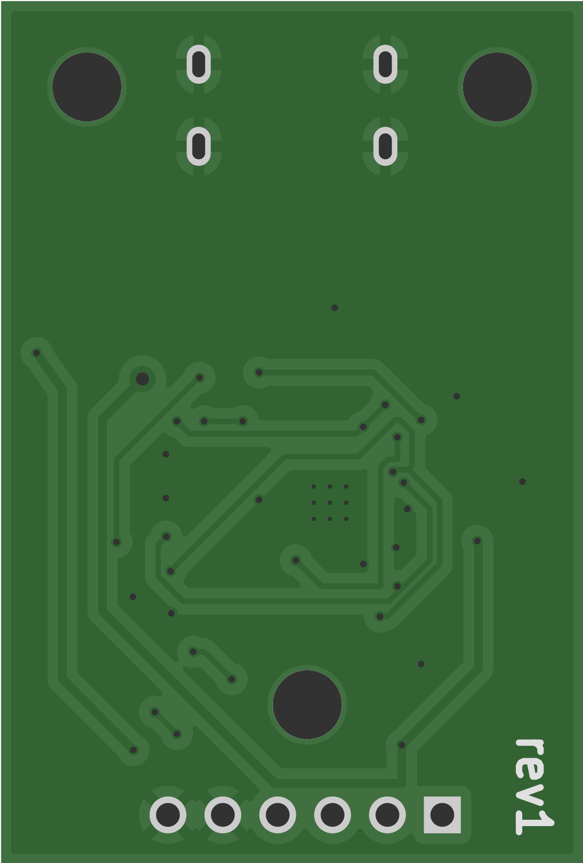
manufacturing/jlcpcb/2026-09-19/board-p/gerber-bottom.png
