Takazudo/zudo-led-lamp/manufacturing/jlcpcb/2026-09-19/swd-adapter/gerber-top.png

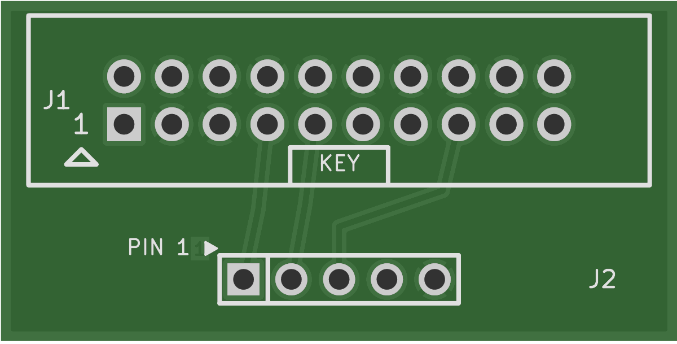
manufacturing/jlcpcb/2026-09-19/swd-adapter/gerber-top.png
